MostlyCoraGrace/EurorackButtonBoard/Docs/Logs/Log-1_001.jpg

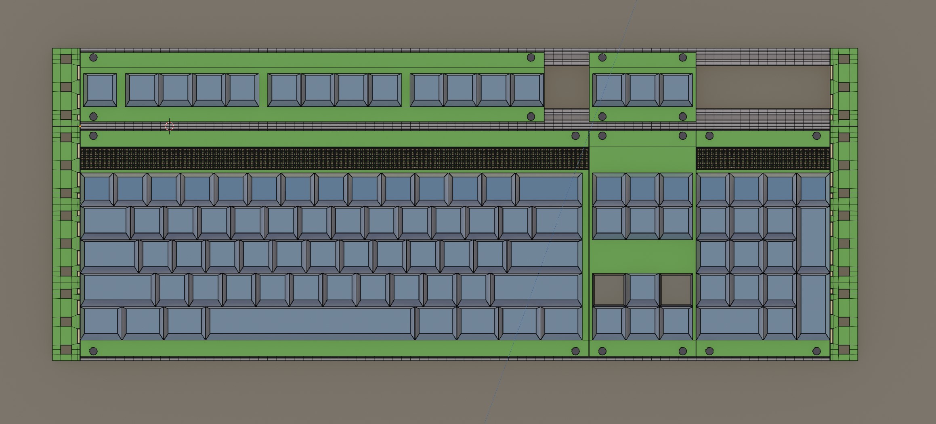
Docs/Logs/Log-1_001.jpg
