MostlyCoraGrace/EurorackButtonBoard/Docs/Logs/Log-2_001.jpg

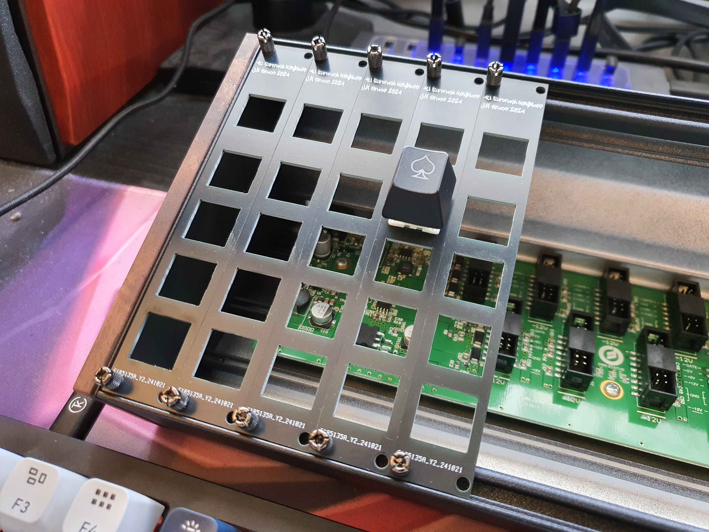
Docs/Logs/Log-2_001.jpg
