MostlyCoraGrace/EurorackButtonBoard/Docs/Logs/Log-3_001.jpg

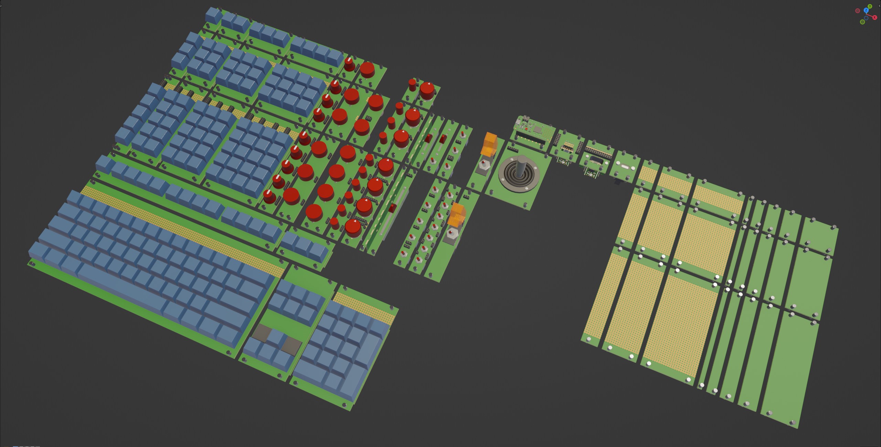
Docs/Logs/Log-3_001.jpg
