MostlyCoraGrace/EurorackButtonBoard/Docs/Logs/Log-3_002.jpg

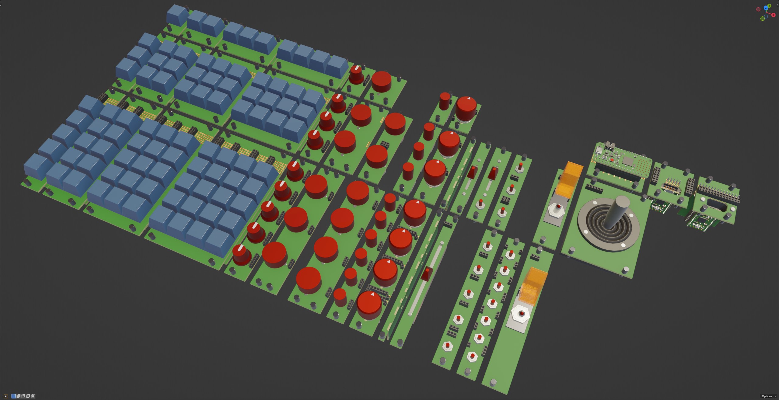
Docs/Logs/Log-3_002.jpg
