MostlyCoraGrace/EurorackButtonBoard/Docs/Logs/Log-4_001.jpg

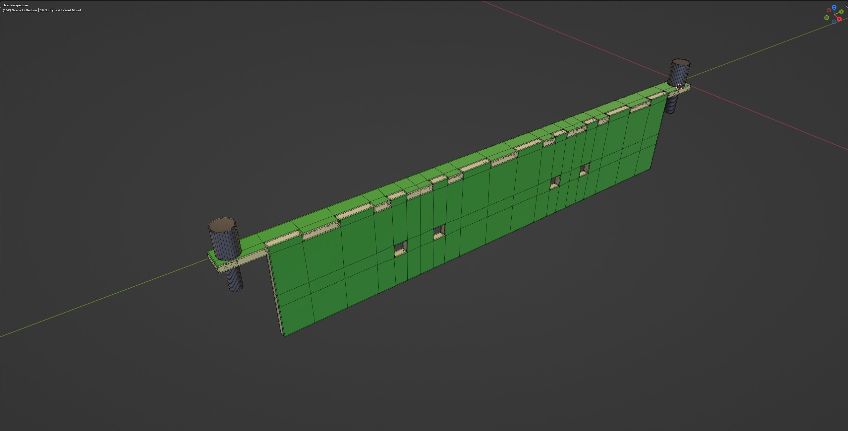
Docs/Logs/Log-4_001.jpg
