MostlyCoraGrace/EurorackButtonBoard/Docs/Logs/Log-4_002.jpg

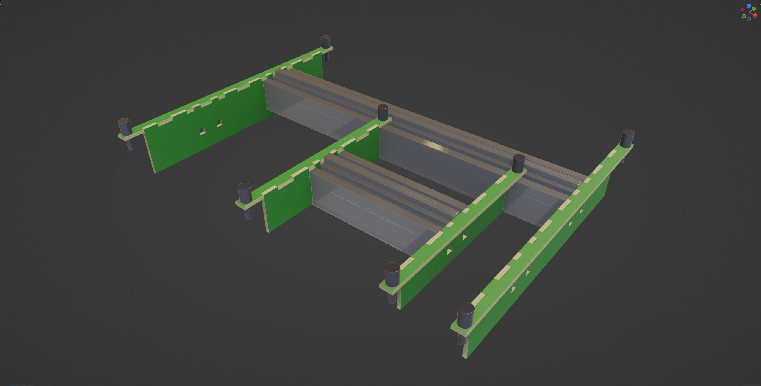
Docs/Logs/Log-4_002.jpg
