MostlyCoraGrace/EurorackButtonBoard/Docs/Logs/Log-4_003.jpg

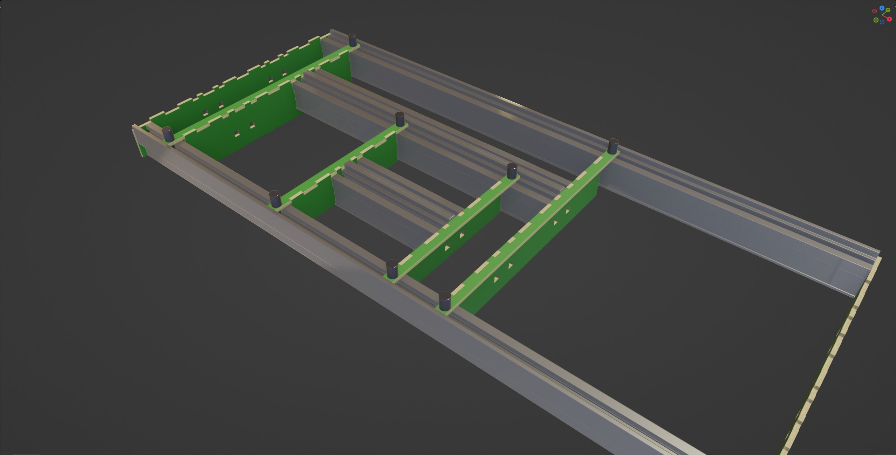
Docs/Logs/Log-4_003.jpg
