MostlyCoraGrace/EurorackButtonBoard/Docs/Logs/Log-6_001.jpg

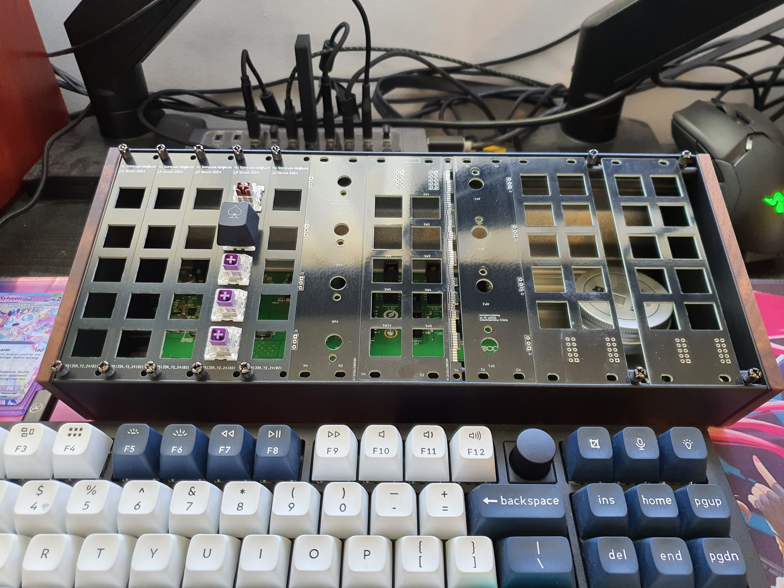
Docs/Logs/Log-6_001.jpg
