MostlyCoraGrace/EurorackButtonBoard/Docs/Logs/Log-6_002.jpg

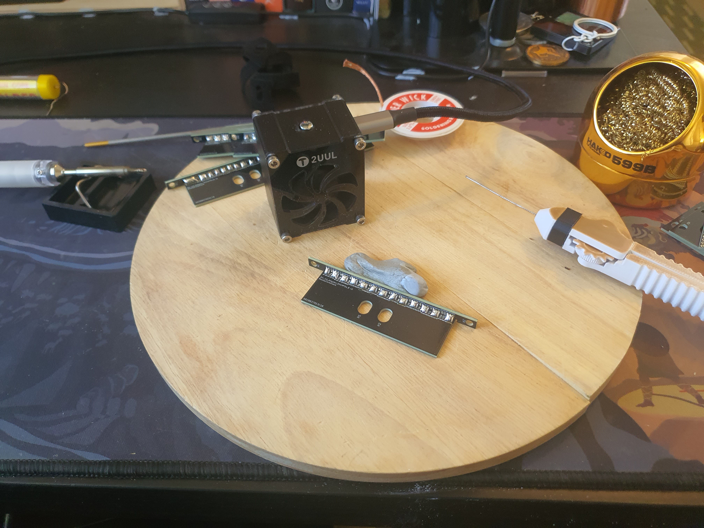
Docs/Logs/Log-6_002.jpg
