MostlyCoraGrace/EurorackButtonBoard/Docs/Logs/Log-6_003.jpg

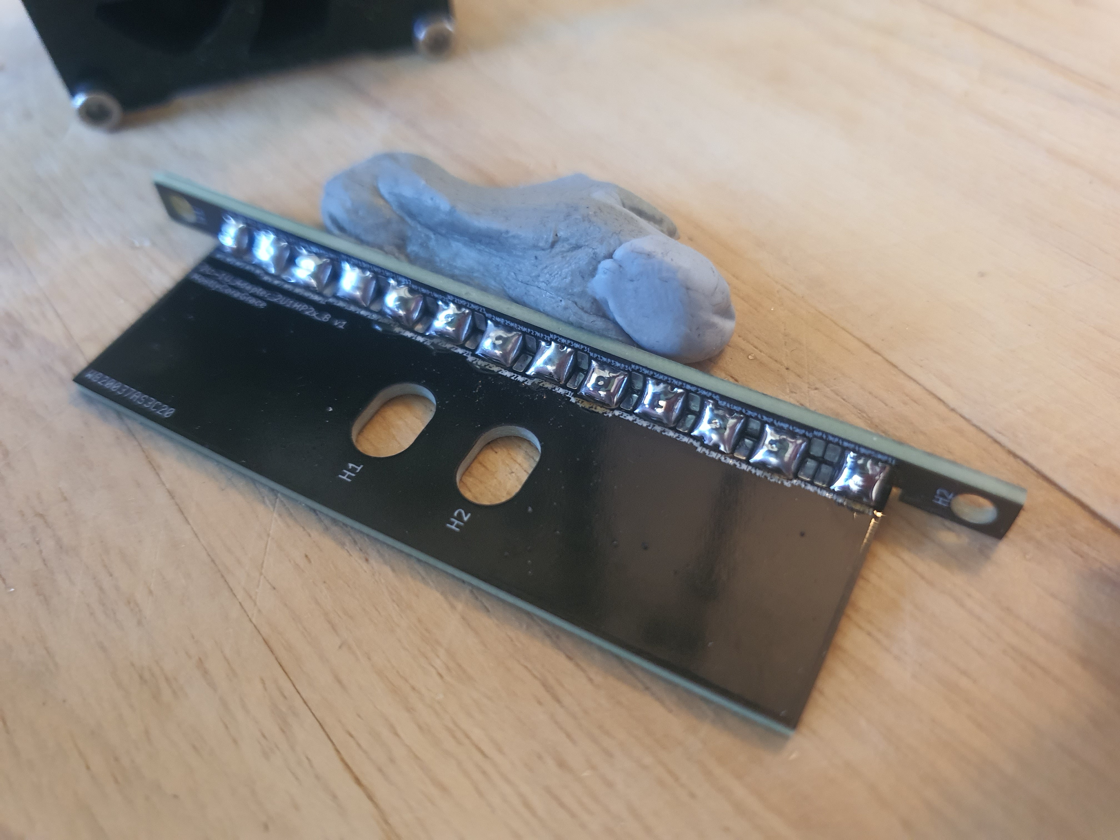
Docs/Logs/Log-6_003.jpg
