MostlyCoraGrace/EurorackButtonBoard/Docs/Logs/Log-6_004.jpg

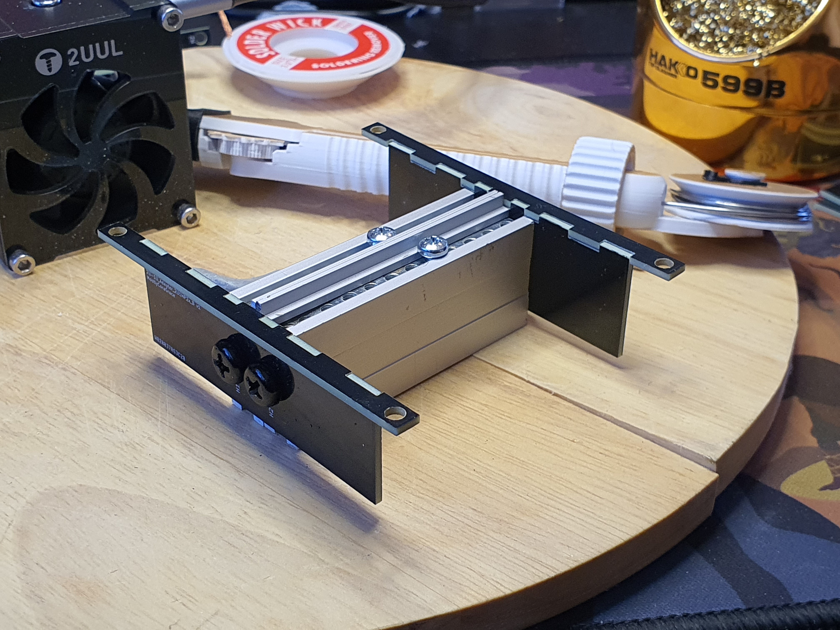
Docs/Logs/Log-6_004.jpg
