MostlyCoraGrace/EurorackButtonBoard/Docs/Logs/Log-6_005.jpg

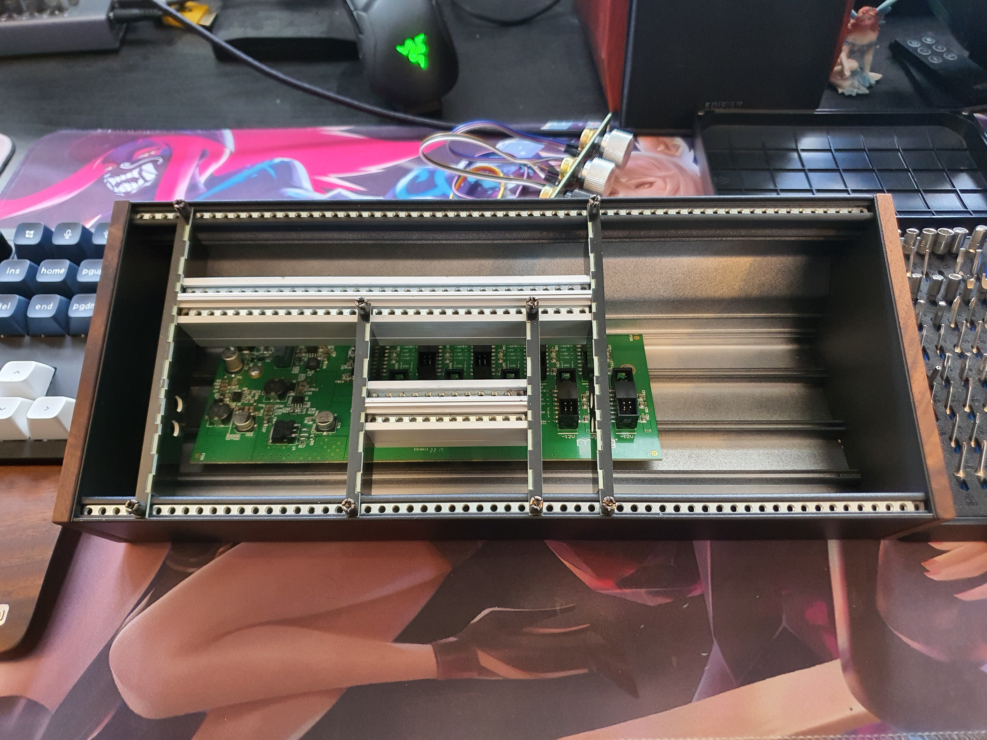
Docs/Logs/Log-6_005.jpg
