MostlyCoraGrace/EurorackButtonBoard/Docs/Logs/Log-6_006.jpg

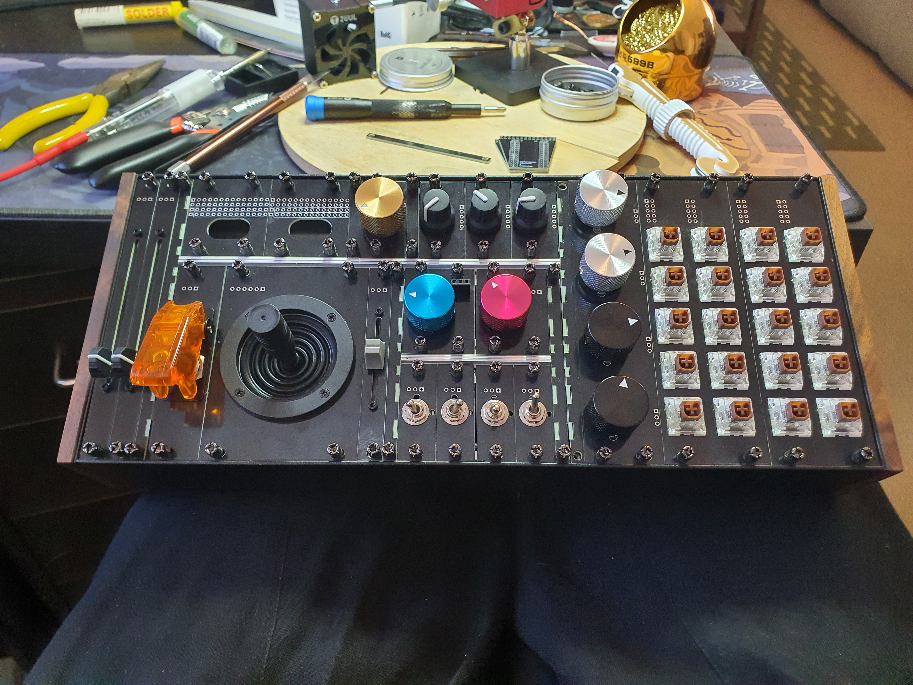
Docs/Logs/Log-6_006.jpg
