MostlyCoraGrace/EurorackButtonBoard/Docs/Logs/Log-6_007.jpg

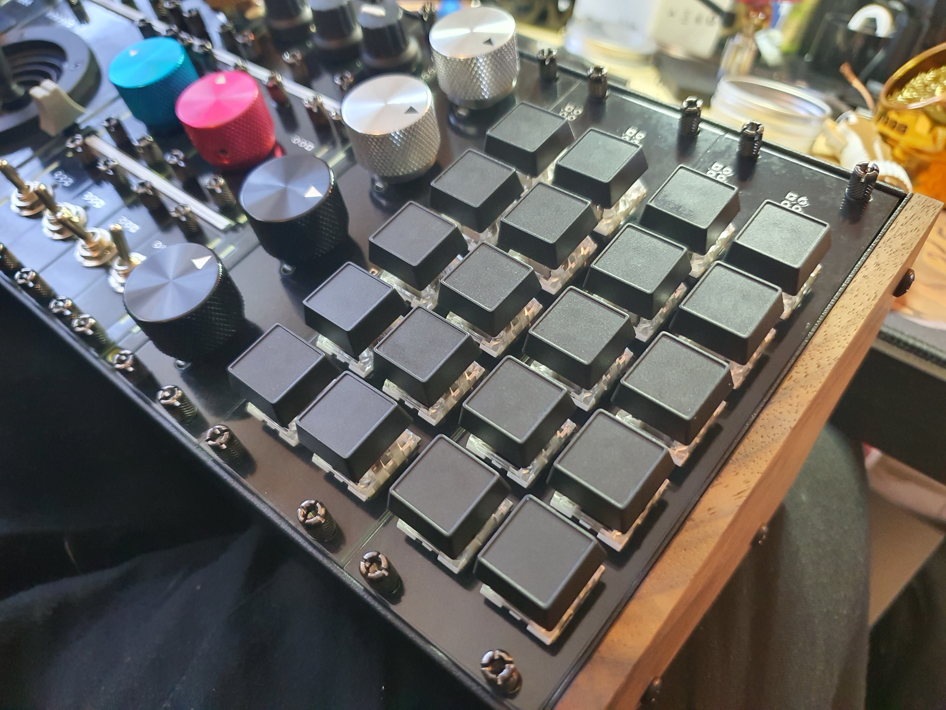
Docs/Logs/Log-6_007.jpg
