MostlyCoraGrace/EurorackButtonBoard/Docs/Logs/Log-6_008.jpg

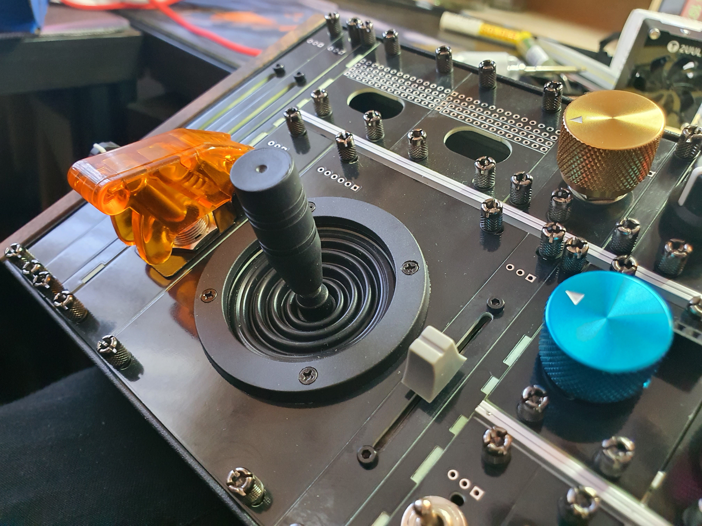
Docs/Logs/Log-6_008.jpg
