MostlyCoraGrace/EurorackButtonBoard/Docs/Logs/Log-6_009.jpg

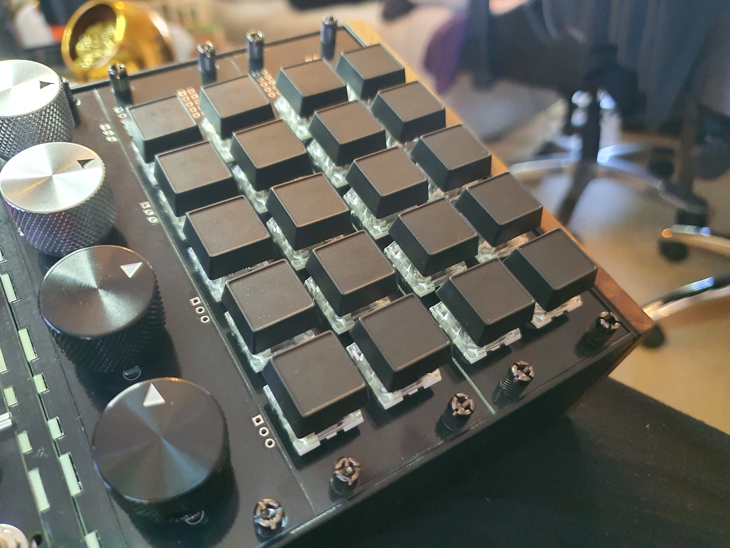
Docs/Logs/Log-6_009.jpg
