MostlyCoraGrace/EurorackButtonBoard/Docs/Logs/Log-6_010.jpg

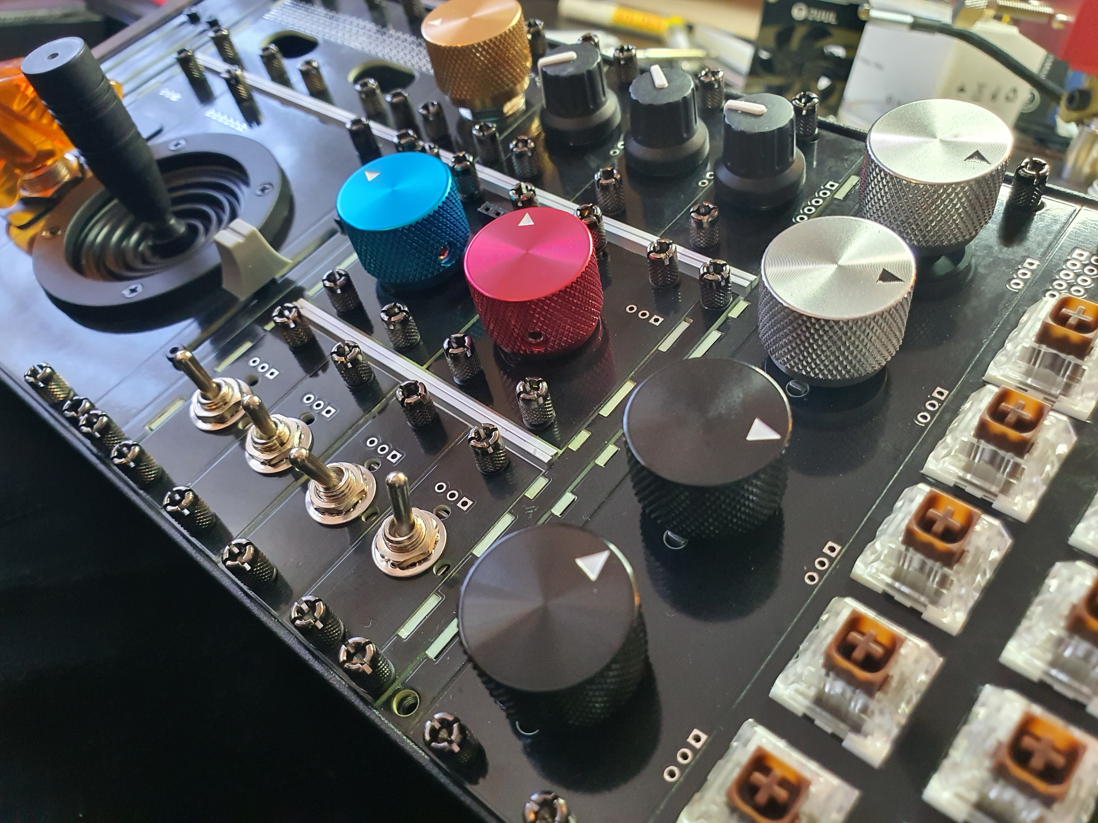
Docs/Logs/Log-6_010.jpg
