MostlyCoraGrace/EurorackButtonBoard/Docs/Logs/Log-6_011.jpg

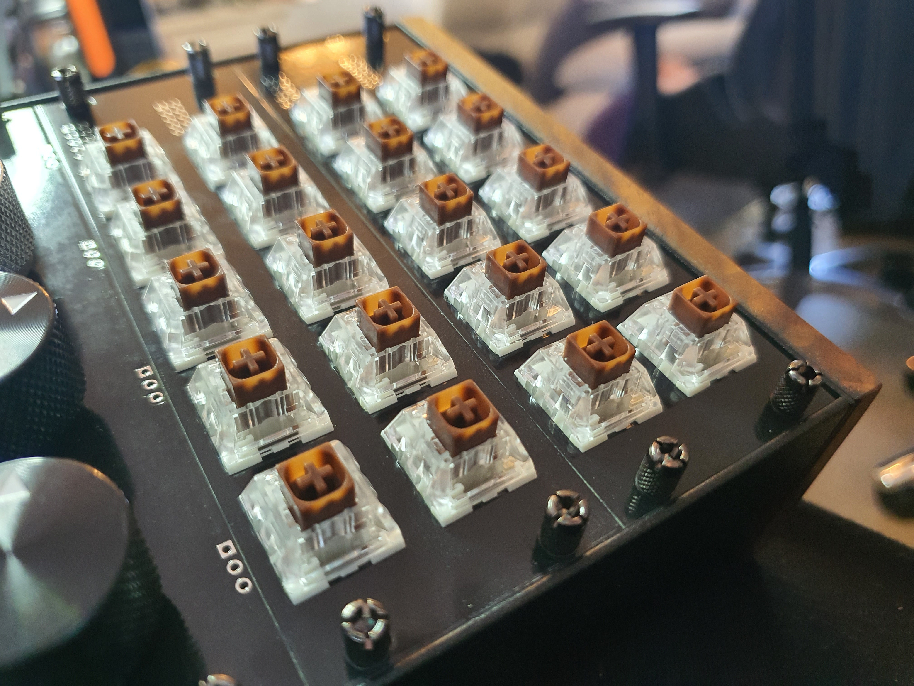
Docs/Logs/Log-6_011.jpg
