MostlyCoraGrace/EurorackButtonBoard/Docs/Logs/Log-6_012.jpg

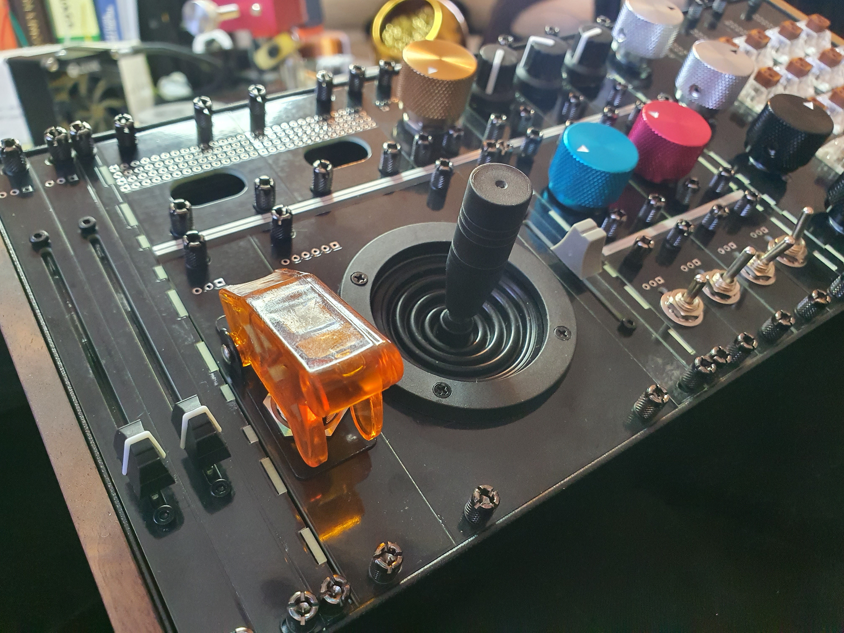
Docs/Logs/Log-6_012.jpg
