MostlyCoraGrace/EurorackButtonBoard/Docs/Logs/Log-6_013.jpg

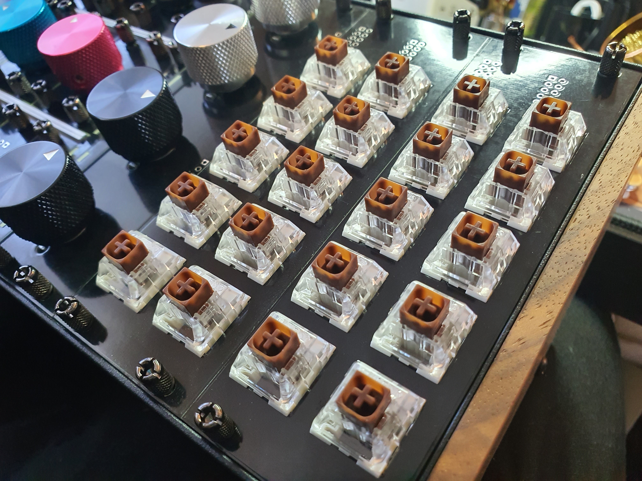
Docs/Logs/Log-6_013.jpg
