MostlyCoraGrace/EurorackButtonBoard/Docs/Logs/Log-6_014.jpg

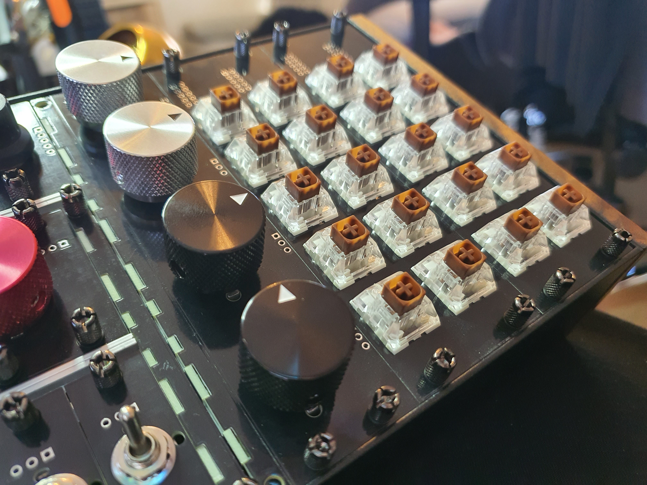
Docs/Logs/Log-6_014.jpg
