MostlyCoraGrace/EurorackButtonBoard/Docs/Logs/Log-6_015.jpg

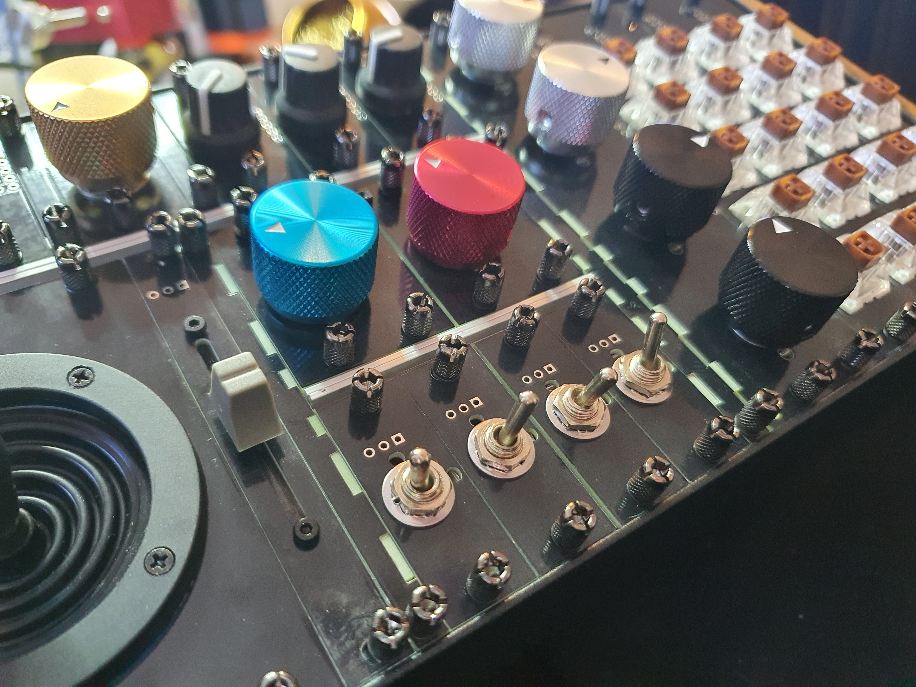
Docs/Logs/Log-6_015.jpg
