MostlyCoraGrace/EurorackButtonBoard/Docs/Logs/Log-7_001.jpg

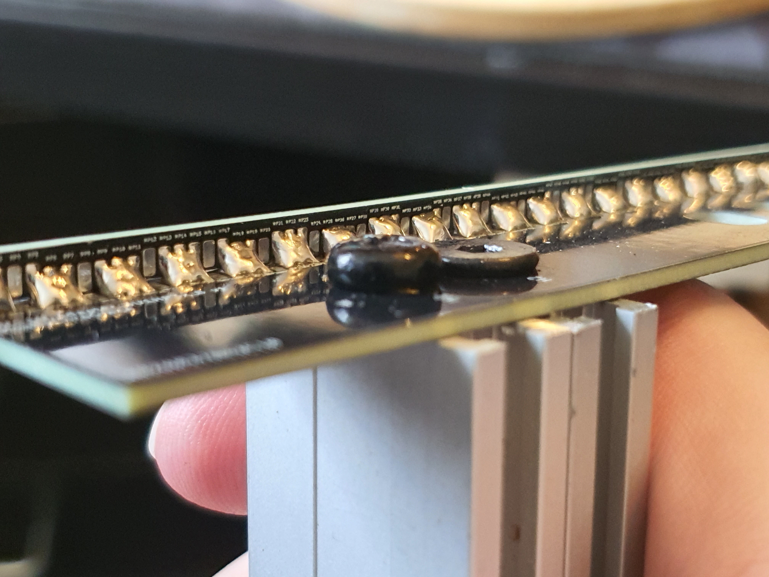
Docs/Logs/Log-7_001.jpg
