MostlyCoraGrace/EurorackButtonBoard/Docs/Logs/Log-7_002.jpg

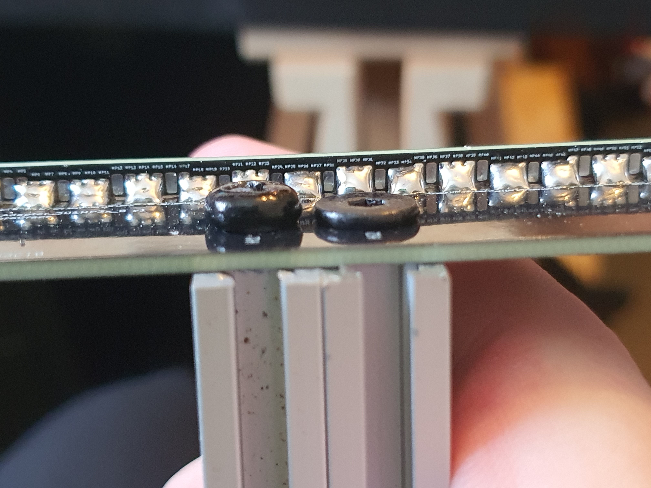
Docs/Logs/Log-7_002.jpg
