MostlyCoraGrace/EurorackButtonBoard/Docs/Logs/Log-7_003.jpg

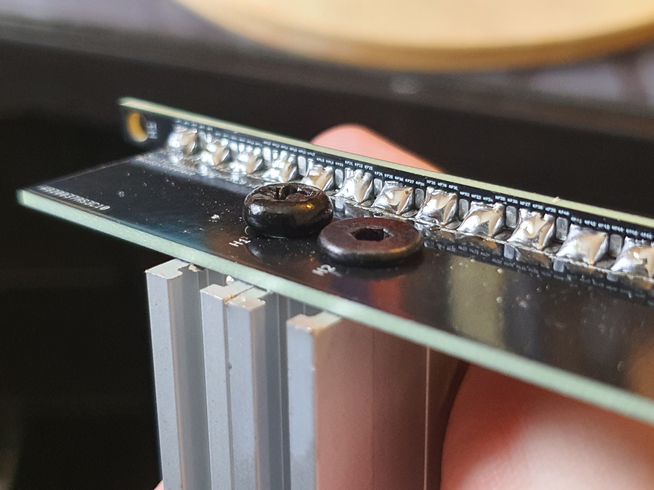
Docs/Logs/Log-7_003.jpg
