MostlyCoraGrace/EurorackButtonBoard/Docs/Logs/Log-7_004.jpg

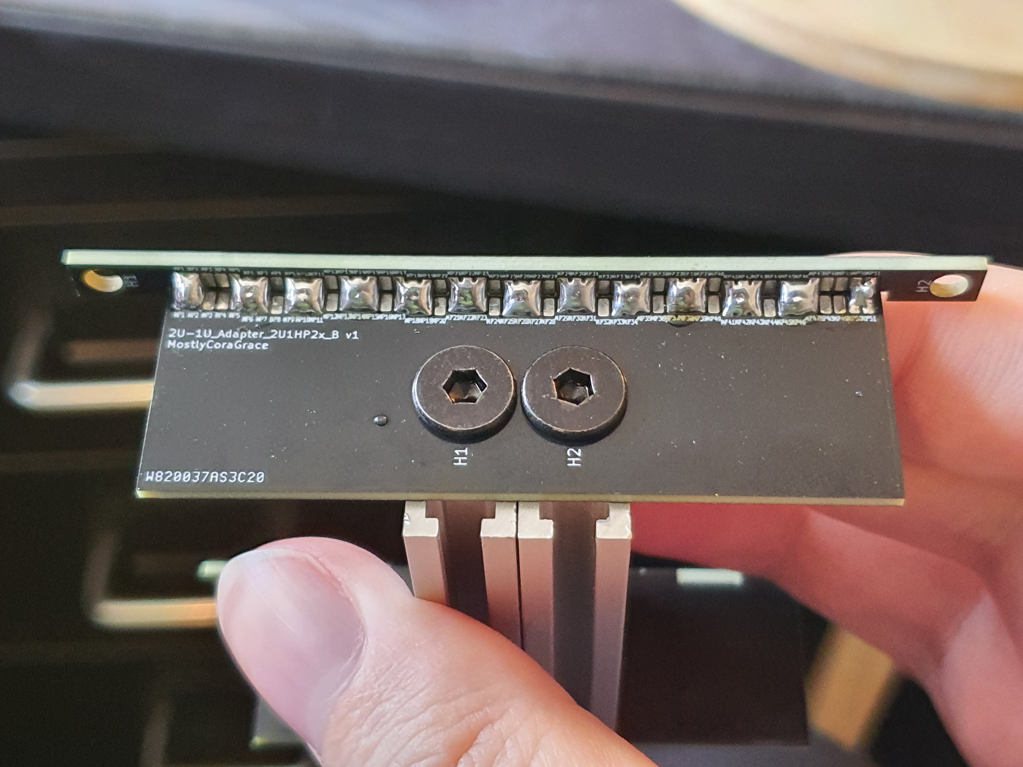
Docs/Logs/Log-7_004.jpg
