MostlyCoraGrace/EurorackButtonBoard/Docs/Logs/Log-7_005.jpg

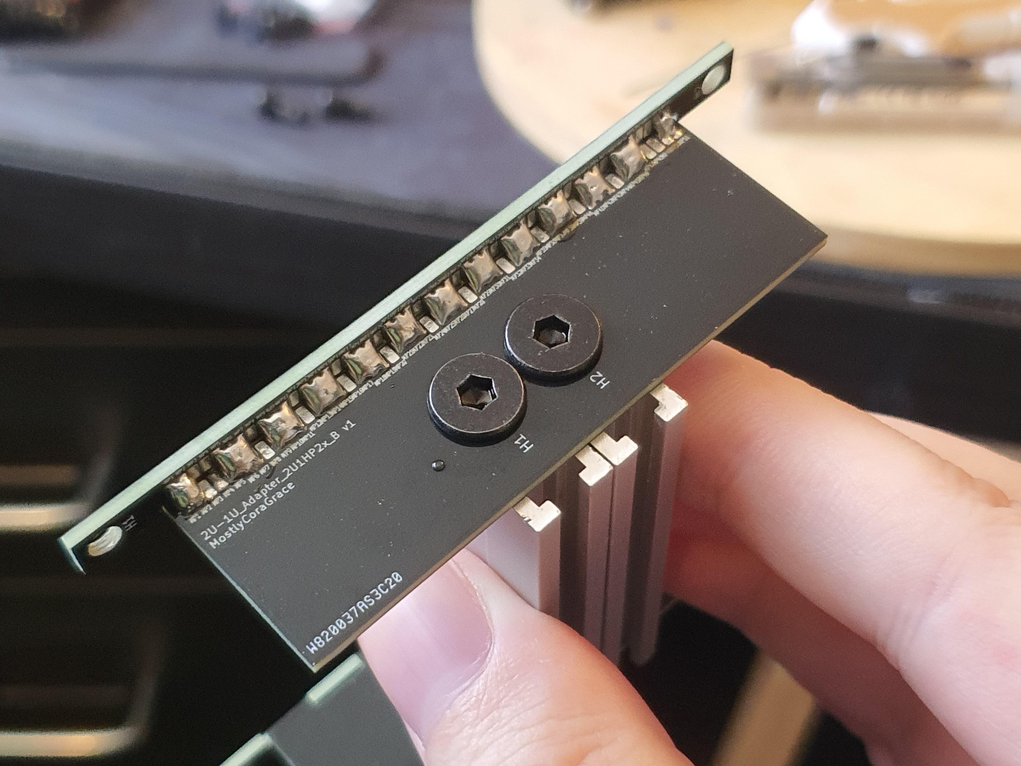
Docs/Logs/Log-7_005.jpg
