MostlyCoraGrace/EurorackButtonBoard/Docs/Logs/Log-7_006.jpg

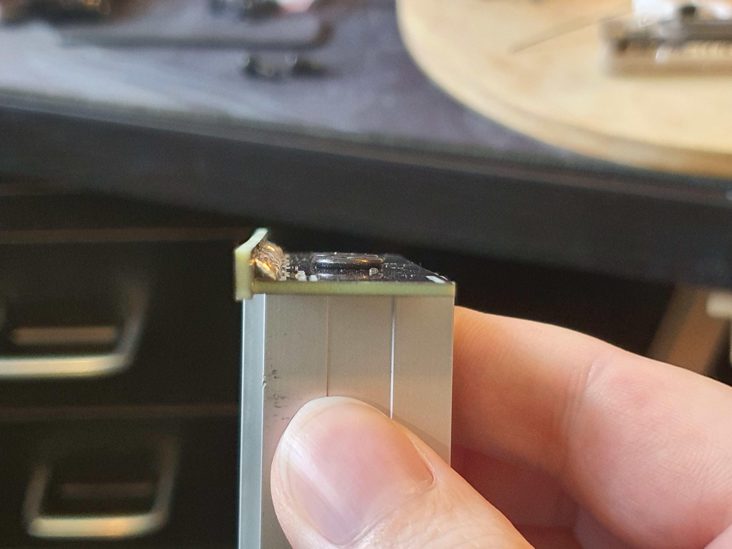
Docs/Logs/Log-7_006.jpg
