MostlyCoraGrace/EurorackButtonBoard/Docs/Logs/Log-7_007.jpg

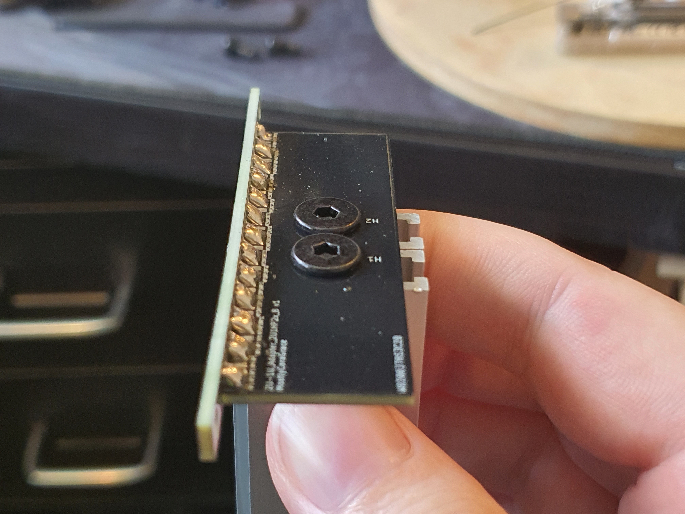
Docs/Logs/Log-7_007.jpg
