MostlyCoraGrace/EurorackButtonBoard/Docs/Logs/Log-8_001.jpg

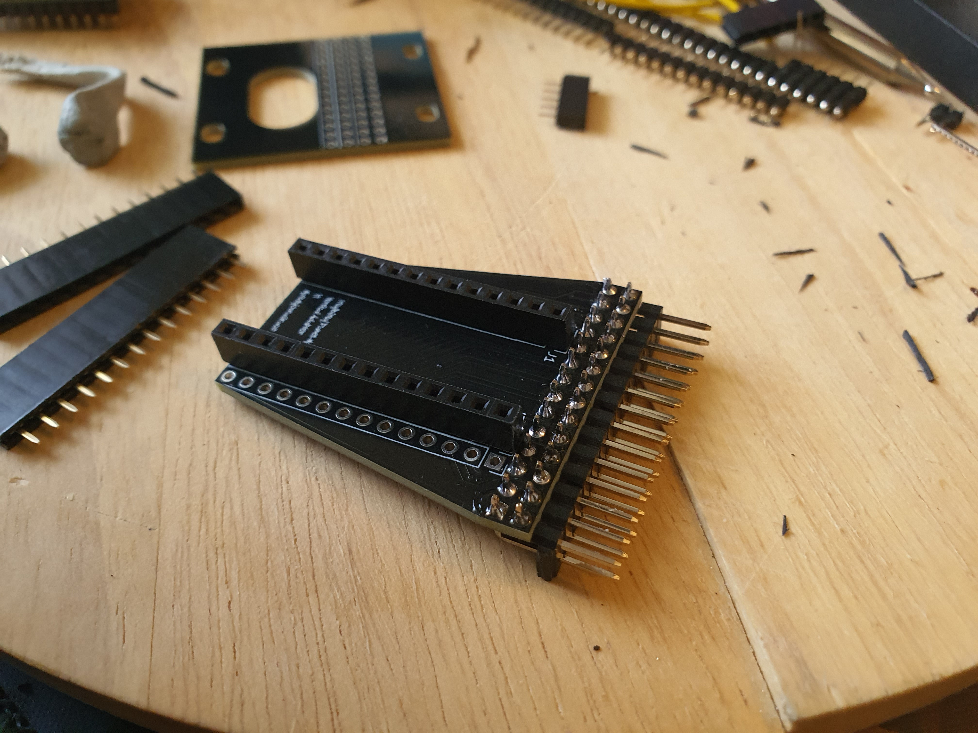
Docs/Logs/Log-8_001.jpg
