MostlyCoraGrace/EurorackButtonBoard/Docs/Logs/Log-8_002.jpg

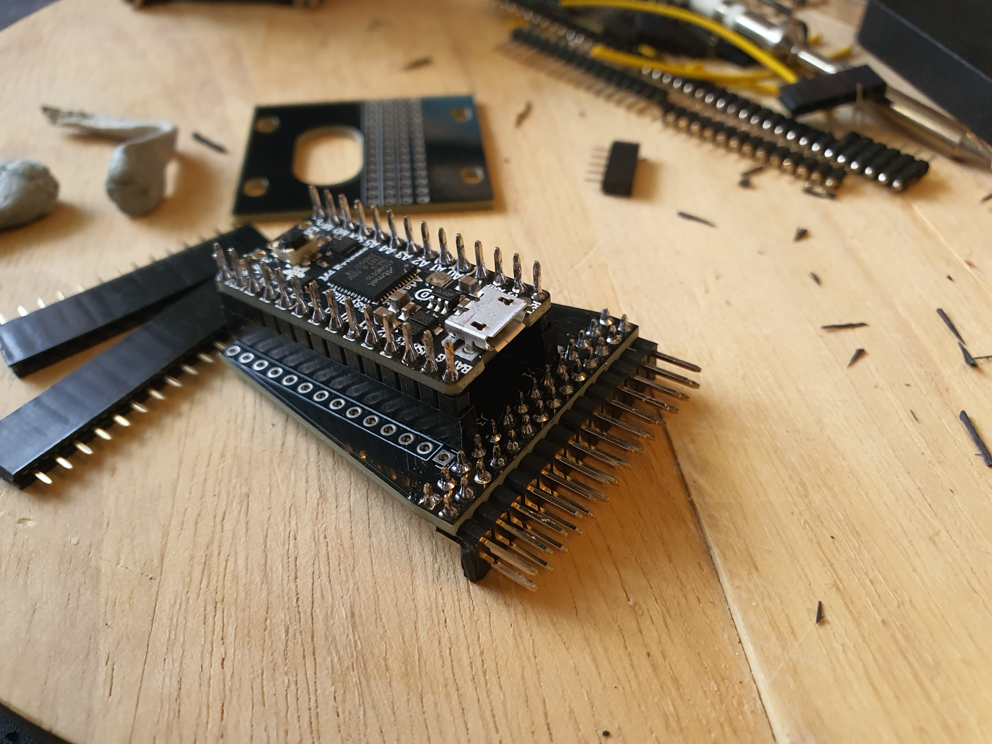
Docs/Logs/Log-8_002.jpg
