MostlyCoraGrace/EurorackButtonBoard/Docs/Logs/Log-8_003.jpg

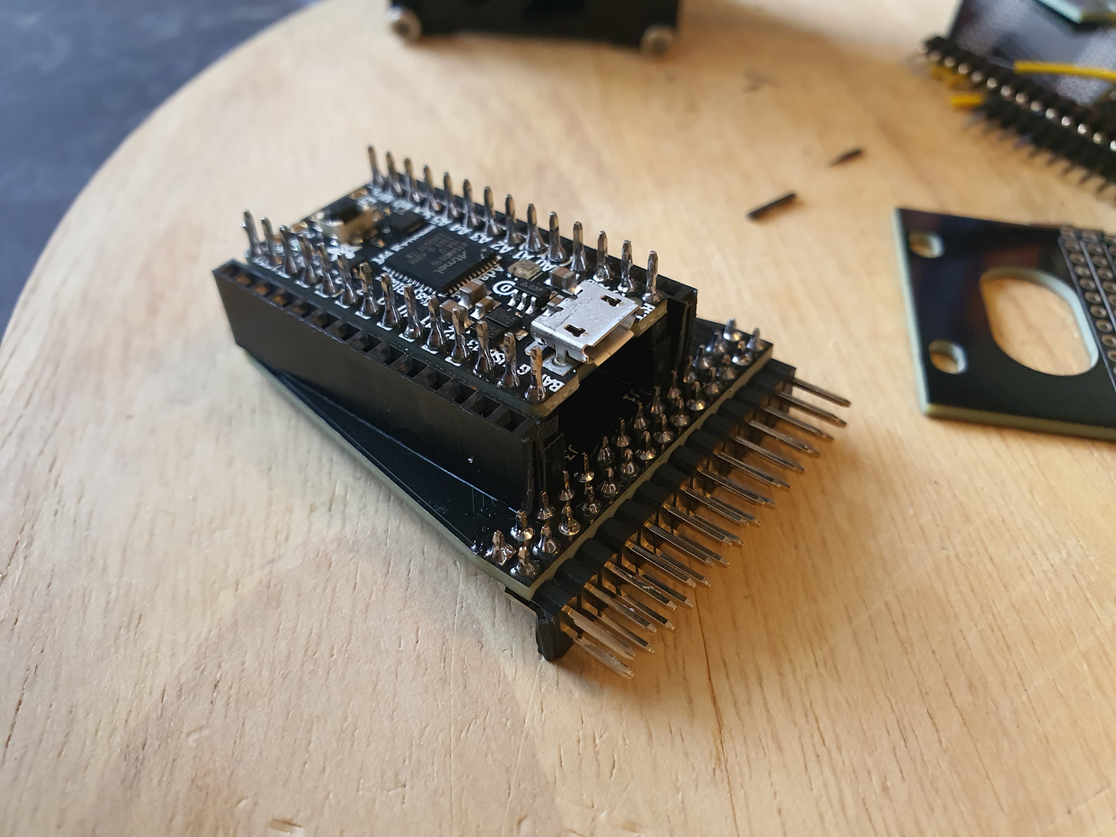
Docs/Logs/Log-8_003.jpg
