MostlyCoraGrace/EurorackButtonBoard/Docs/Logs/Log-8_004.jpg

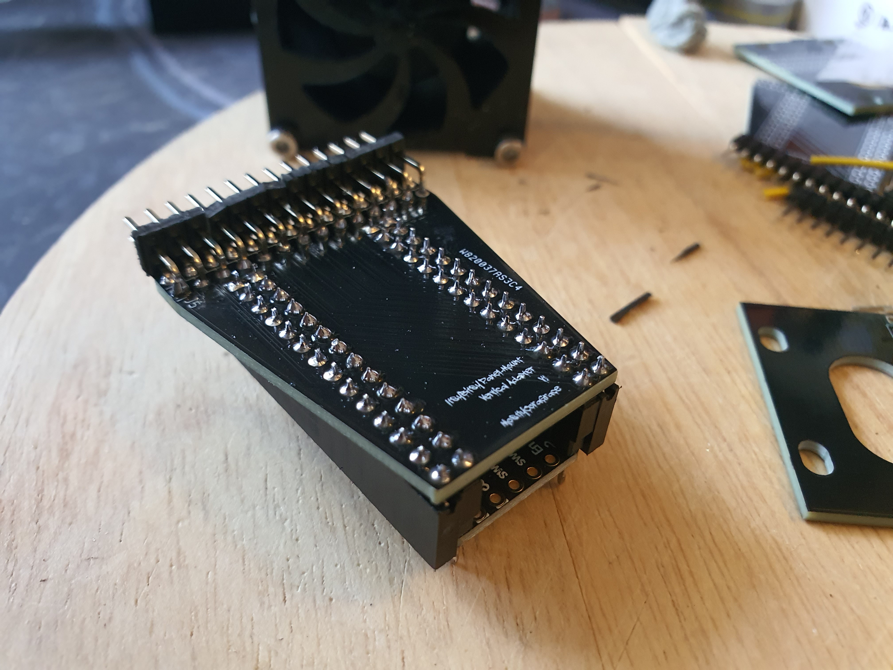
Docs/Logs/Log-8_004.jpg
