MostlyCoraGrace/EurorackButtonBoard/Docs/Logs/Log-8_005.jpg

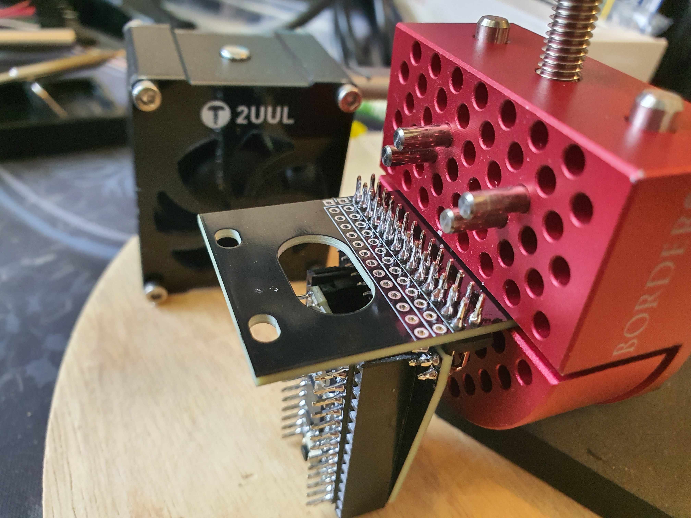
Docs/Logs/Log-8_005.jpg
