MostlyCoraGrace/EurorackButtonBoard/Docs/Logs/Log-8_006.jpg

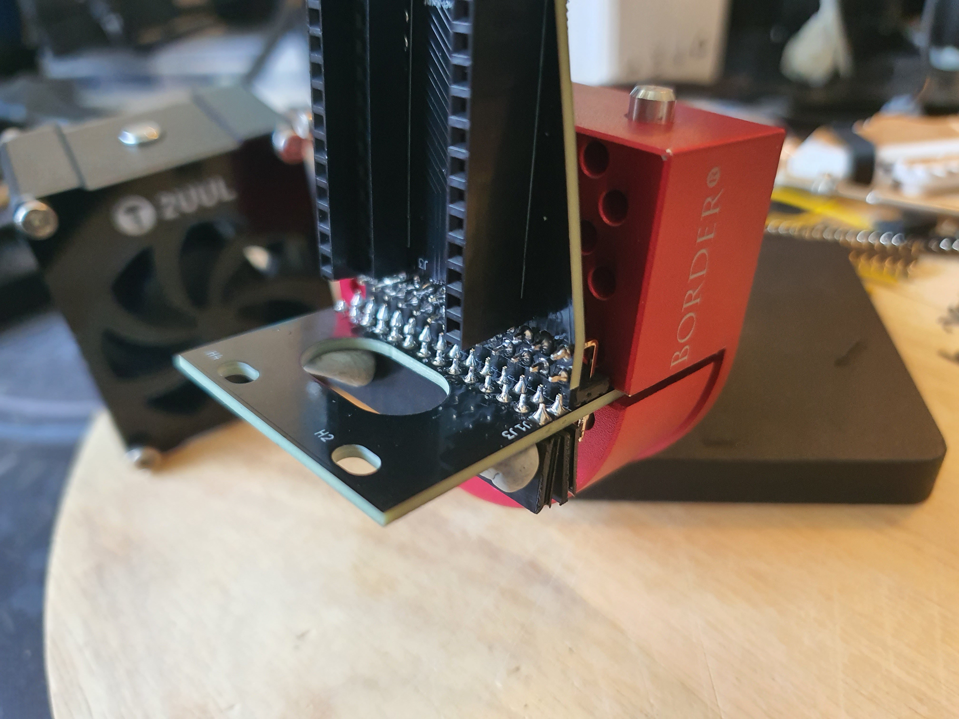
Docs/Logs/Log-8_006.jpg
