MostlyCoraGrace/EurorackButtonBoard/Docs/Logs/Log-8_007.jpg

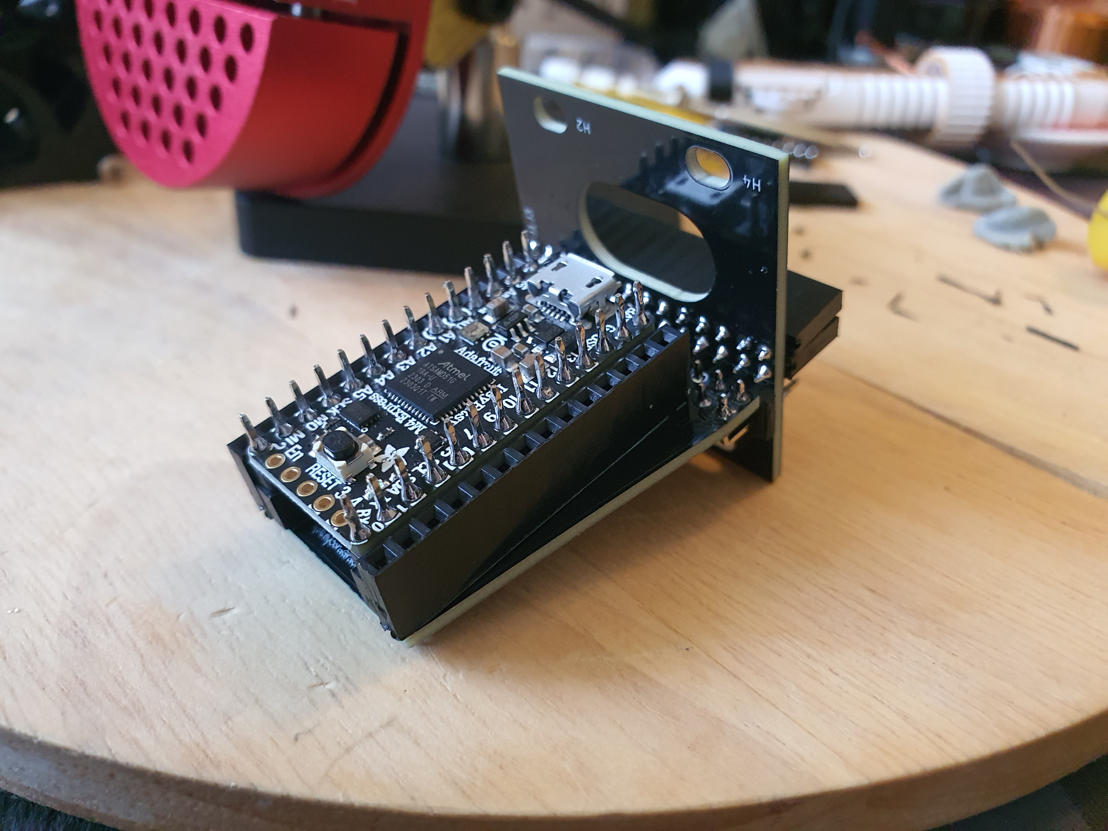
Docs/Logs/Log-8_007.jpg
