MostlyCoraGrace/EurorackButtonBoard/Docs/Logs/Log-8_008.jpg

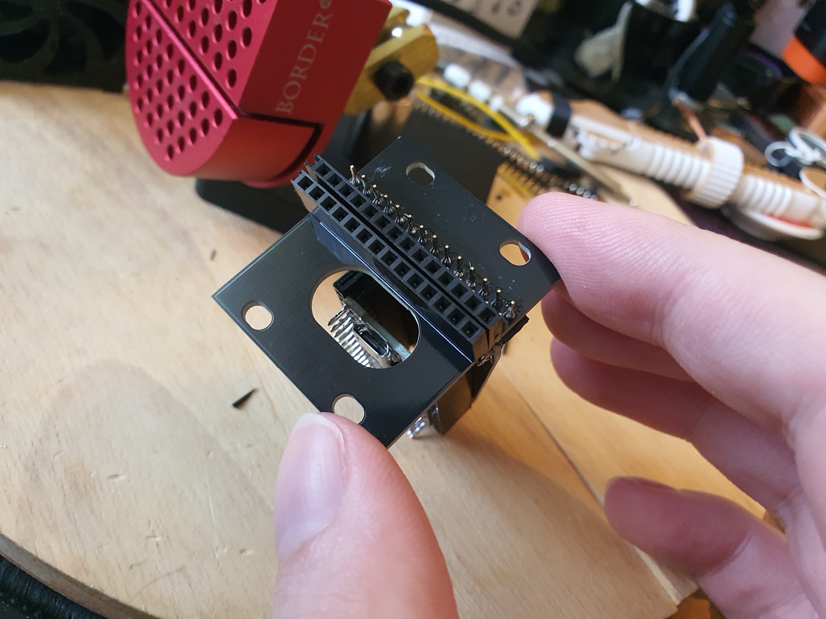
Docs/Logs/Log-8_008.jpg
