MostlyCoraGrace/EurorackButtonBoard/Docs/Logs/Log-8_009.jpg

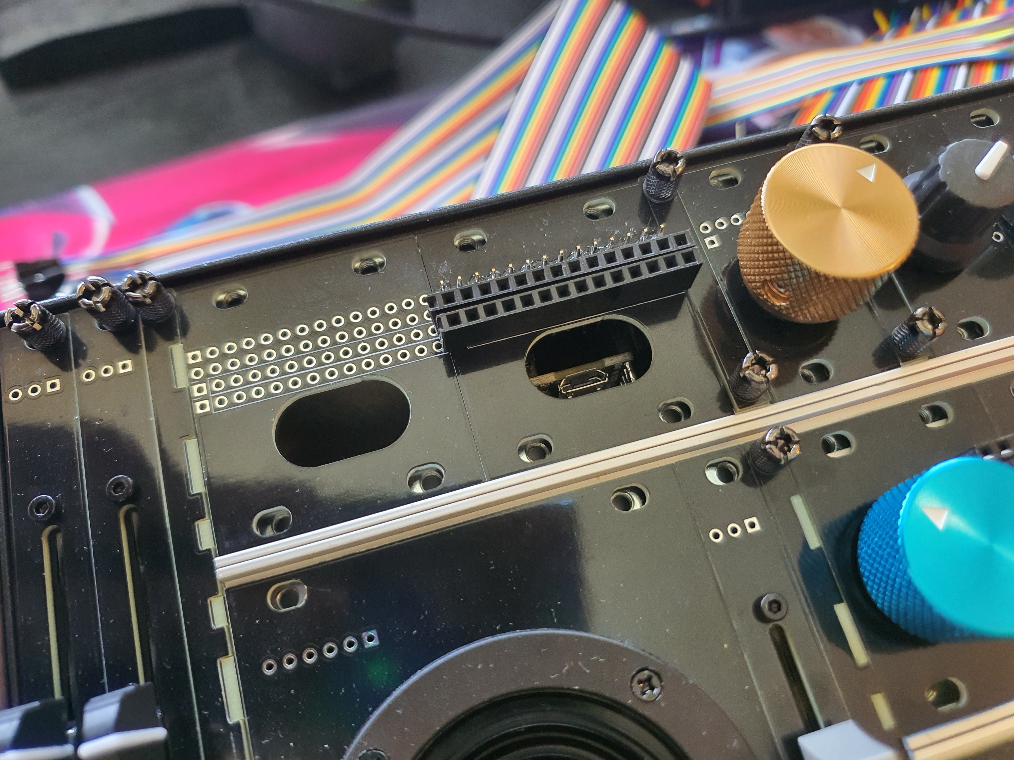
Docs/Logs/Log-8_009.jpg
