MostlyCoraGrace/EurorackButtonBoard/Docs/Logs/Log-8_010.jpg

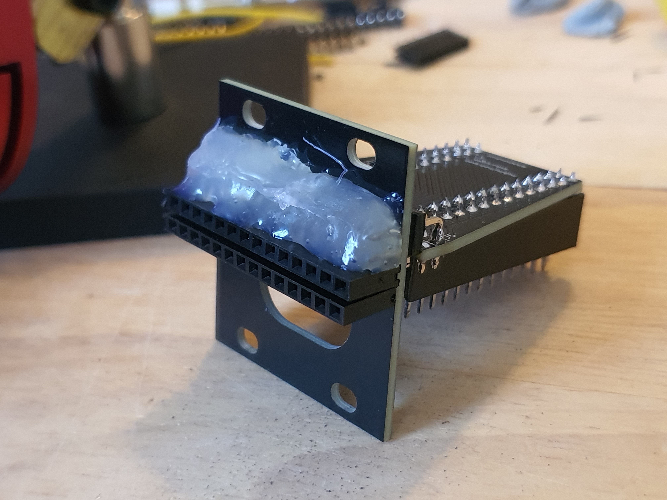
Docs/Logs/Log-8_010.jpg
