MostlyCoraGrace/EurorackButtonBoard/Docs/Logs/Log-8_011.jpg

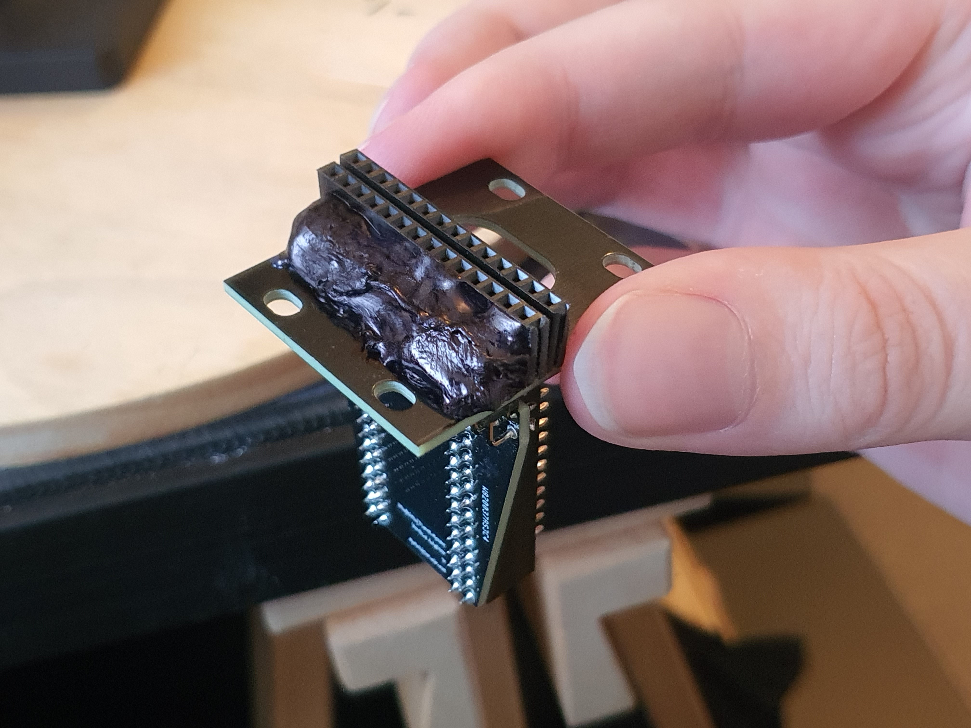
Docs/Logs/Log-8_011.jpg
