MostlyCoraGrace/EurorackButtonBoard/Docs/Logs/Log-9_001.jpg

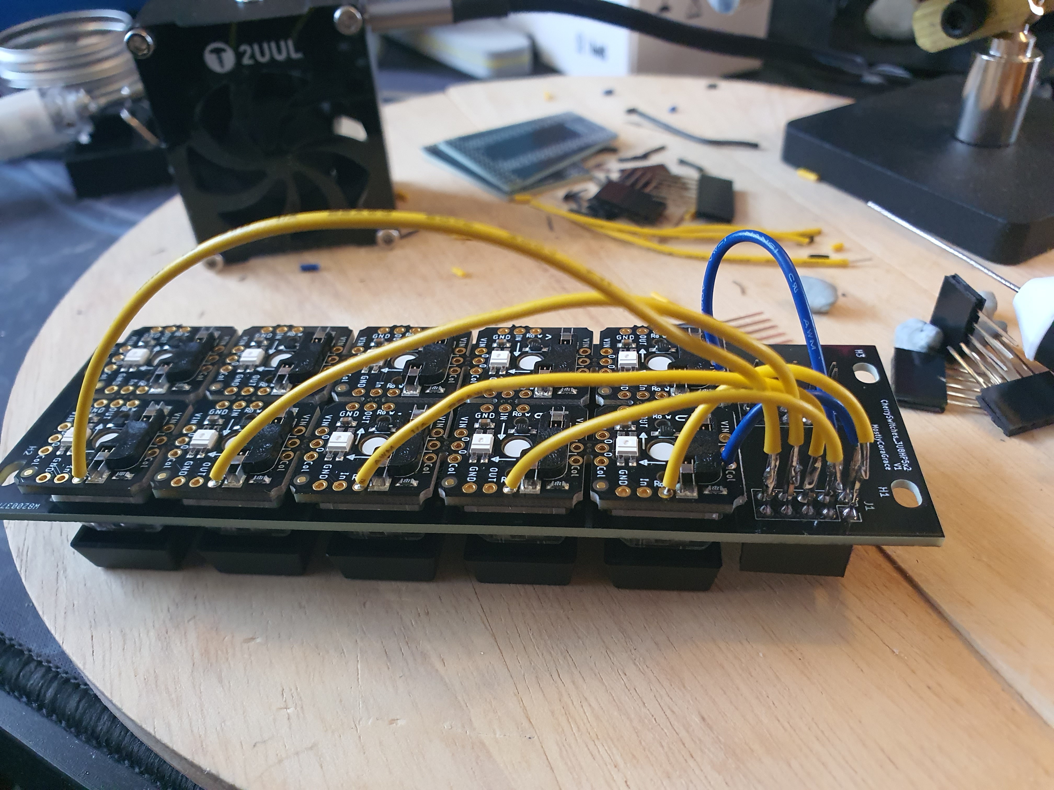
Docs/Logs/Log-9_001.jpg
