MostlyCoraGrace/EurorackButtonBoard/Docs/Logs/Log-9_002.jpg

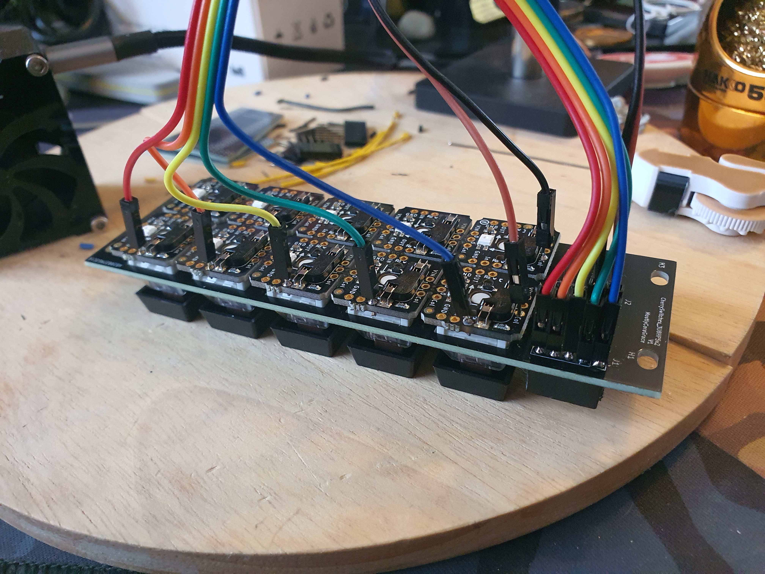
Docs/Logs/Log-9_002.jpg
