MostlyCoraGrace/EurorackButtonBoard/Docs/Logs/Log-9_003.jpg

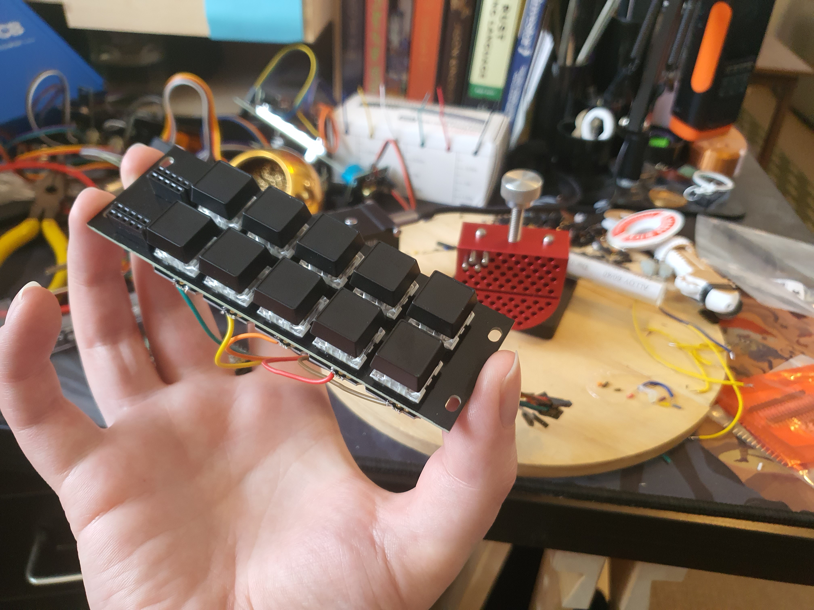
Docs/Logs/Log-9_003.jpg
