MostlyCoraGrace/EurorackButtonBoard/Docs/Logs/Log-9_004.jpg

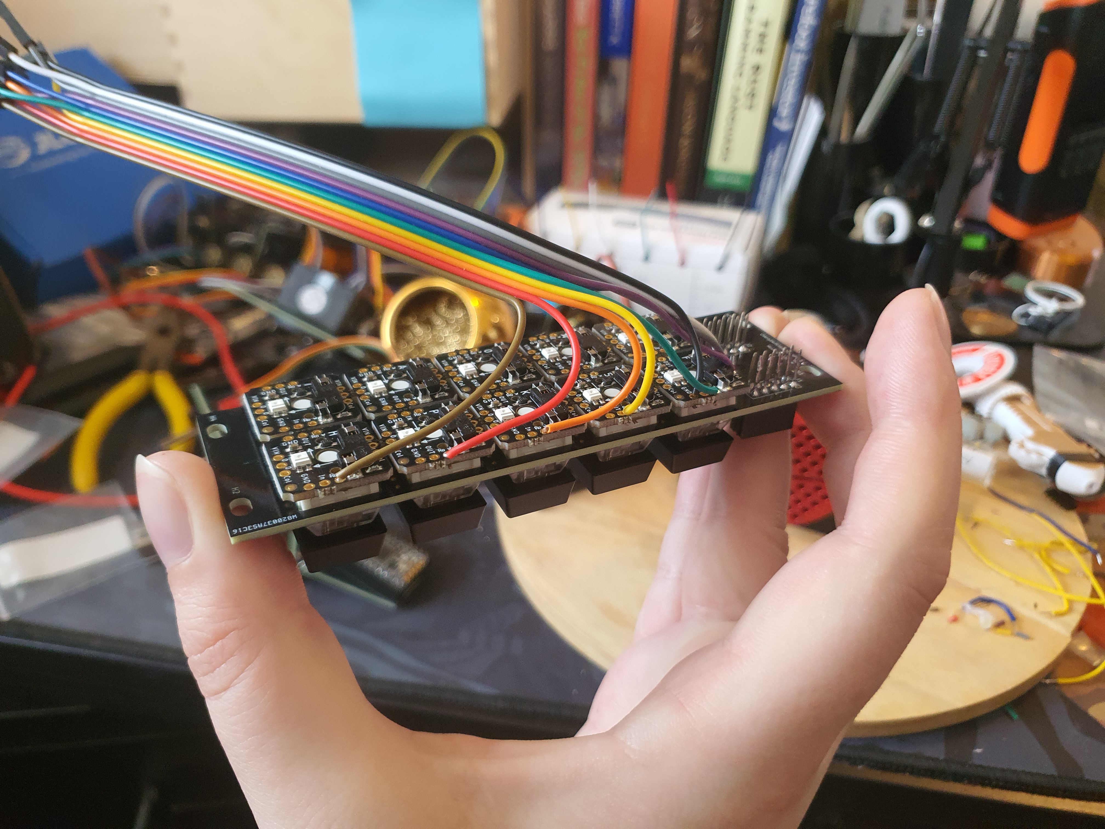
Docs/Logs/Log-9_004.jpg
