MostlyCoraGrace/EurorackButtonBoard/Docs/Logs/Log-9_005.jpg

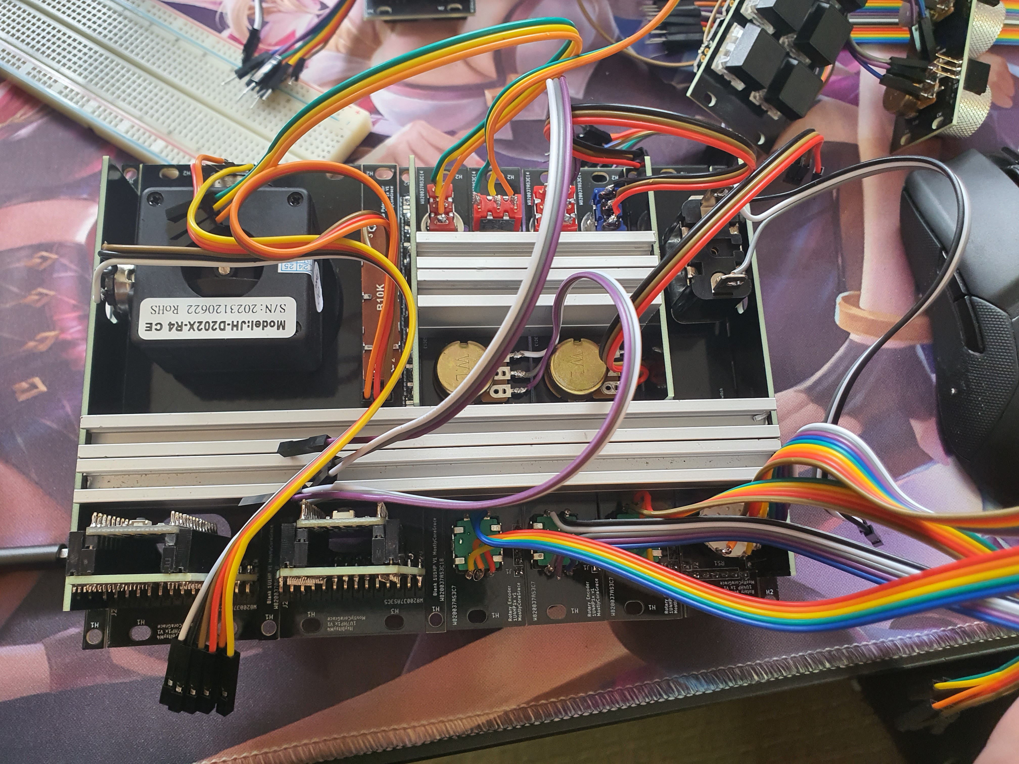
Docs/Logs/Log-9_005.jpg
