MostlyCoraGrace/EurorackButtonBoard/Docs/Logs/Log-9_006.jpg

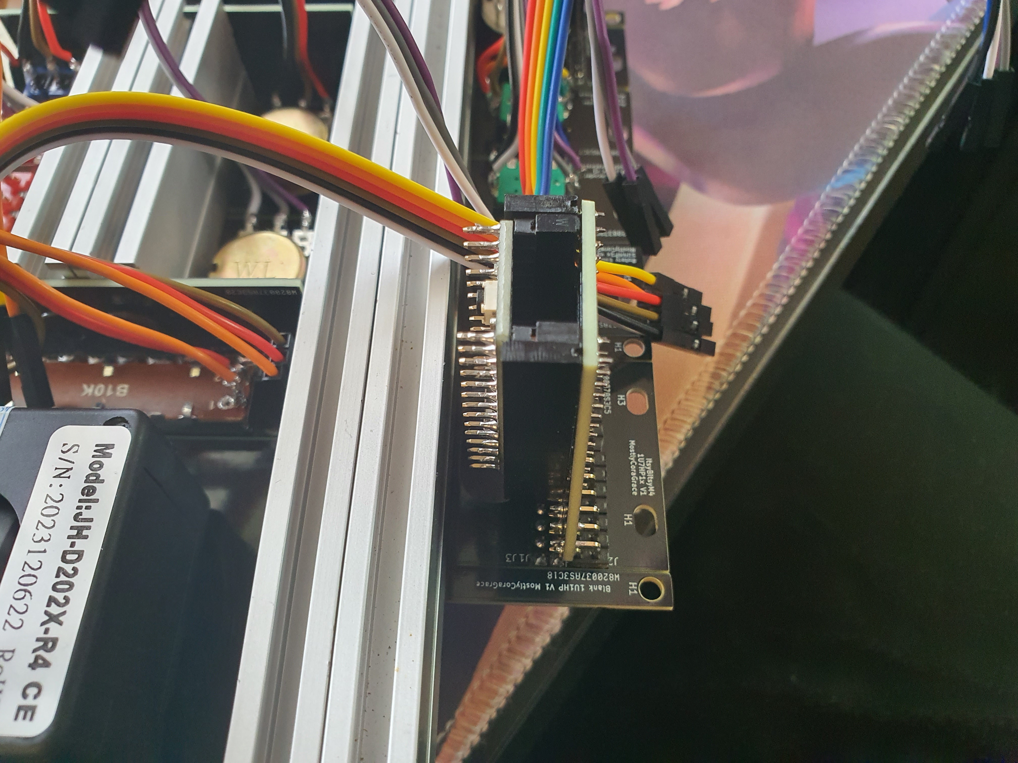
Docs/Logs/Log-9_006.jpg
