MostlyCoraGrace/EurorackButtonBoard/Docs/Logs/Log-9_007.jpg

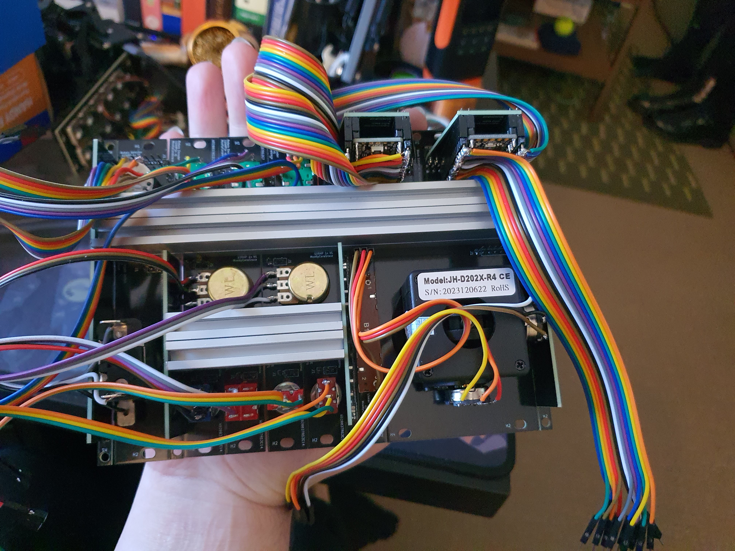
Docs/Logs/Log-9_007.jpg
