MostlyCoraGrace/EurorackButtonBoard/Docs/Logs/Log-9_008.jpg

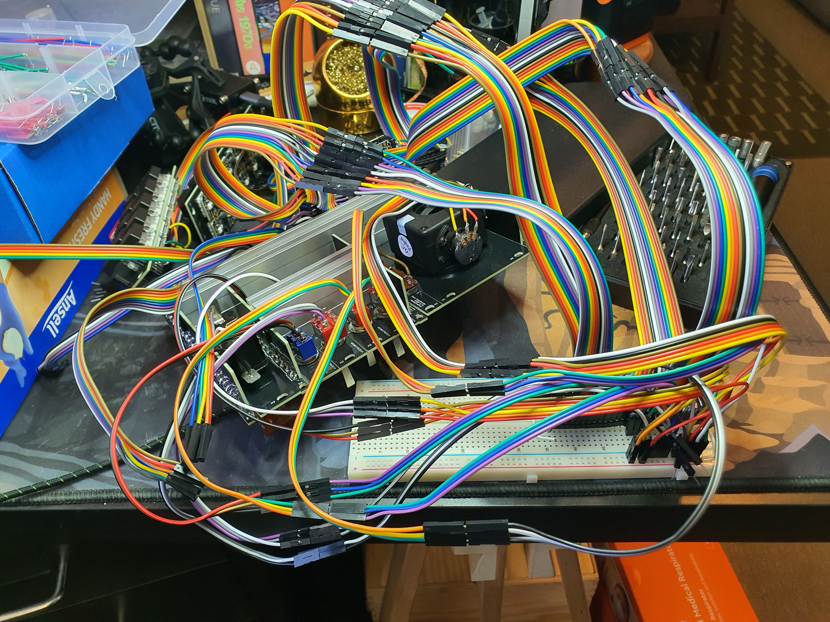
Docs/Logs/Log-9_008.jpg
