MostlyCoraGrace/EurorackButtonBoard/Docs/Logs/Log-9_009.jpg

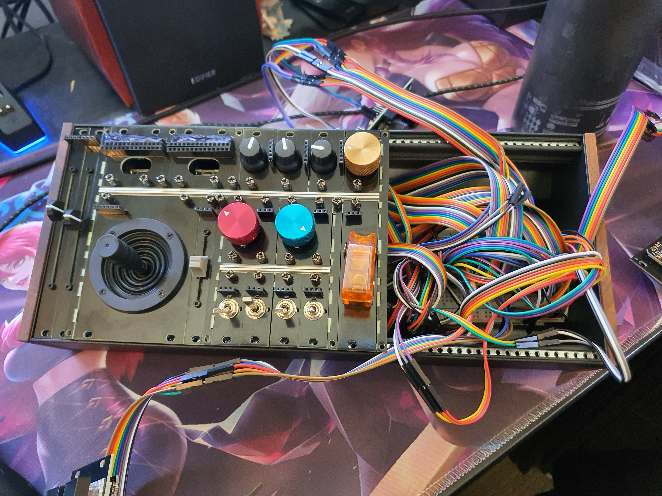
Docs/Logs/Log-9_009.jpg
