MostlyCoraGrace/EurorackButtonBoard/Docs/Logs/Log-9_010.jpg

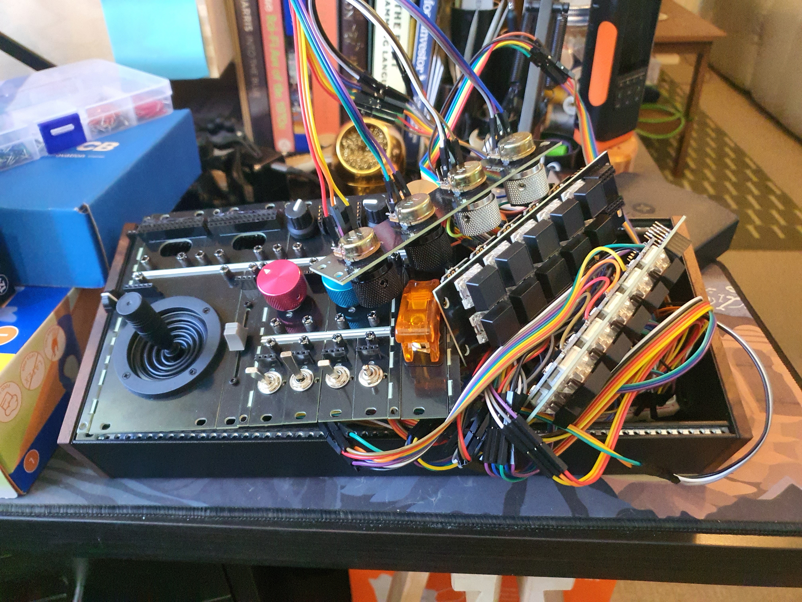
Docs/Logs/Log-9_010.jpg
