MostlyCoraGrace/EurorackButtonBoard/Docs/Logs/Log-9_011.jpg

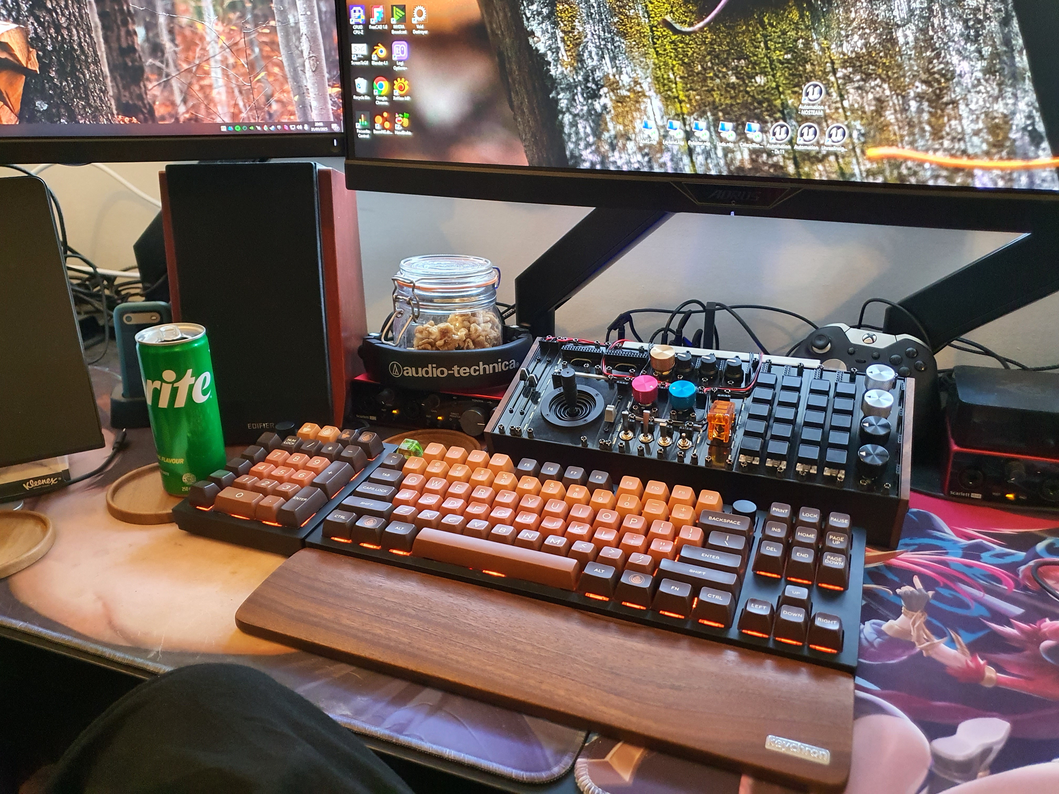
Docs/Logs/Log-9_011.jpg
