MostlyCoraGrace/EurorackButtonBoard/Docs/Logs/Log-10_001.png

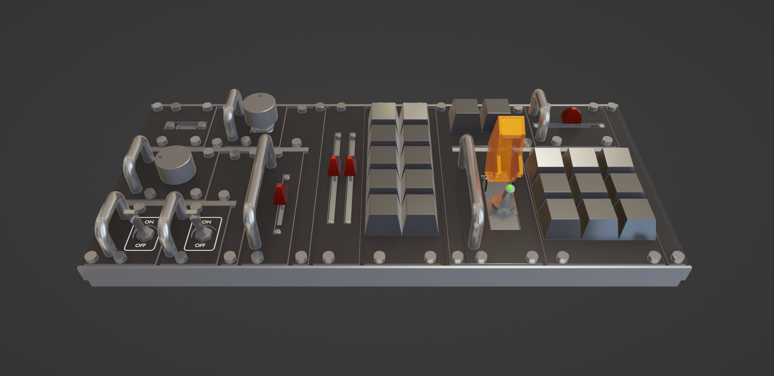
Docs/Logs/Log-10_001.png
