MostlyCoraGrace/EurorackButtonBoard/Docs/Logs/Log-10_002.jpg

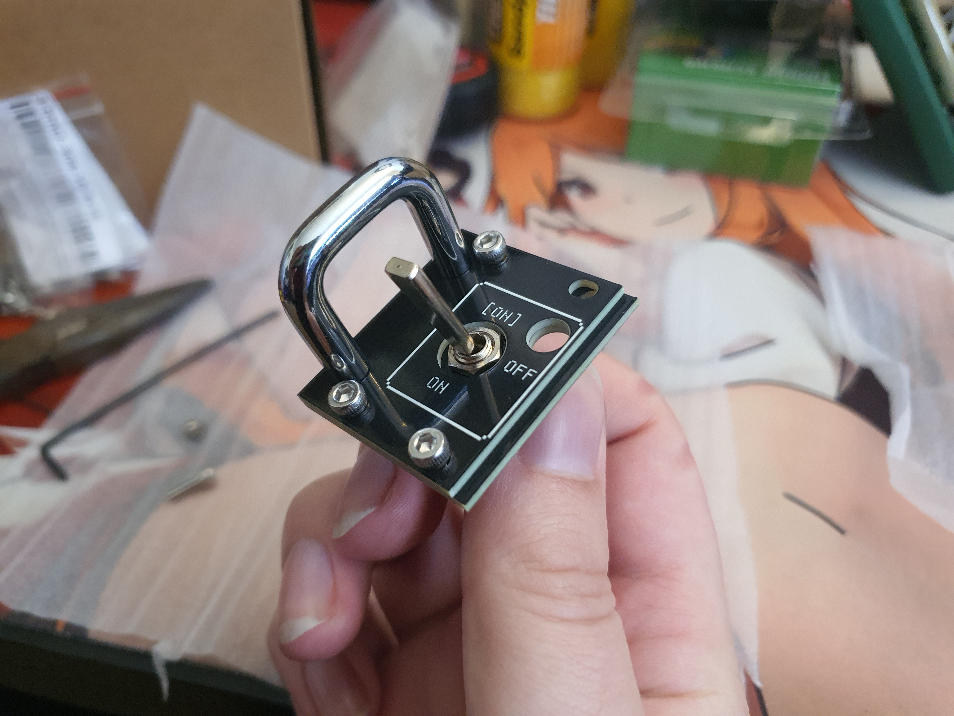
Docs/Logs/Log-10_002.jpg
