MostlyCoraGrace/EurorackButtonBoard/Docs/Logs/Log-10_003.jpg

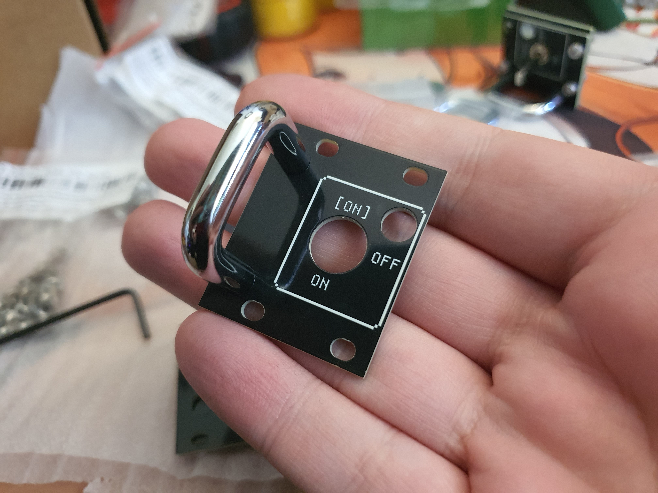
Docs/Logs/Log-10_003.jpg
