MostlyCoraGrace/EurorackButtonBoard/Docs/Logs/Log-10_004.jpg

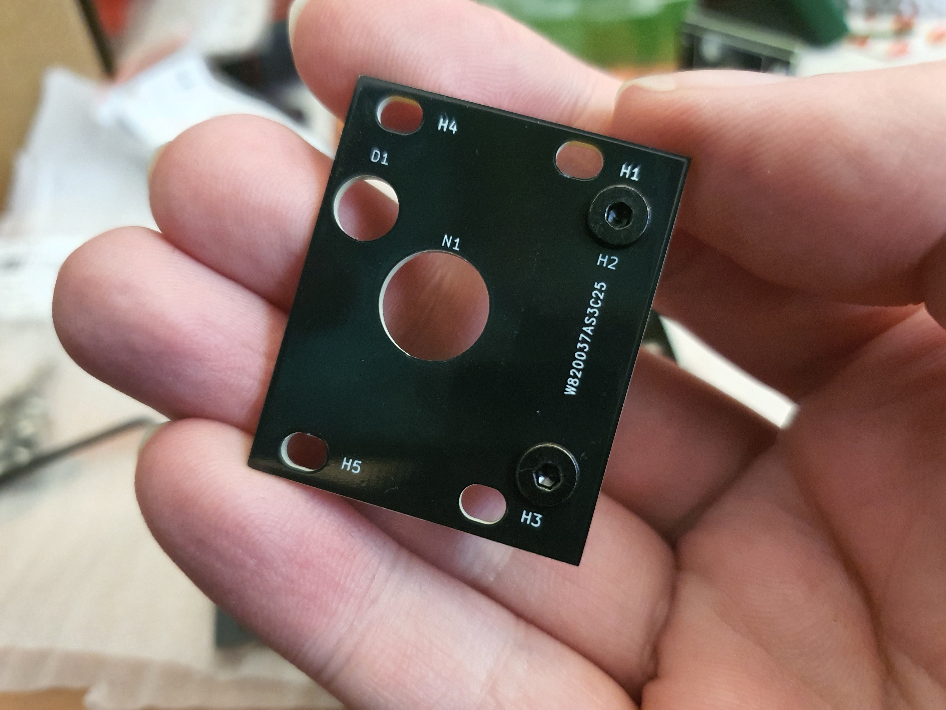
Docs/Logs/Log-10_004.jpg
