MostlyCoraGrace/EurorackButtonBoard/Docs/Logs/Log-10_005.jpg

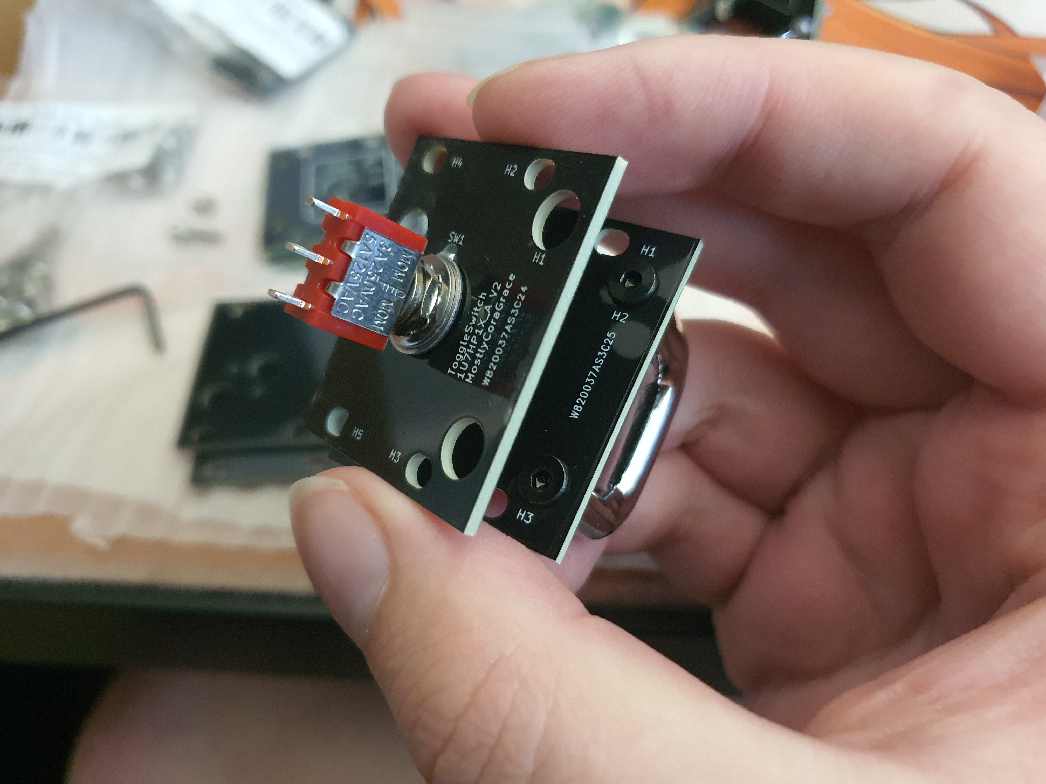
Docs/Logs/Log-10_005.jpg
