MostlyCoraGrace/EurorackButtonBoard/Docs/Logs/Log-10_006.jpg

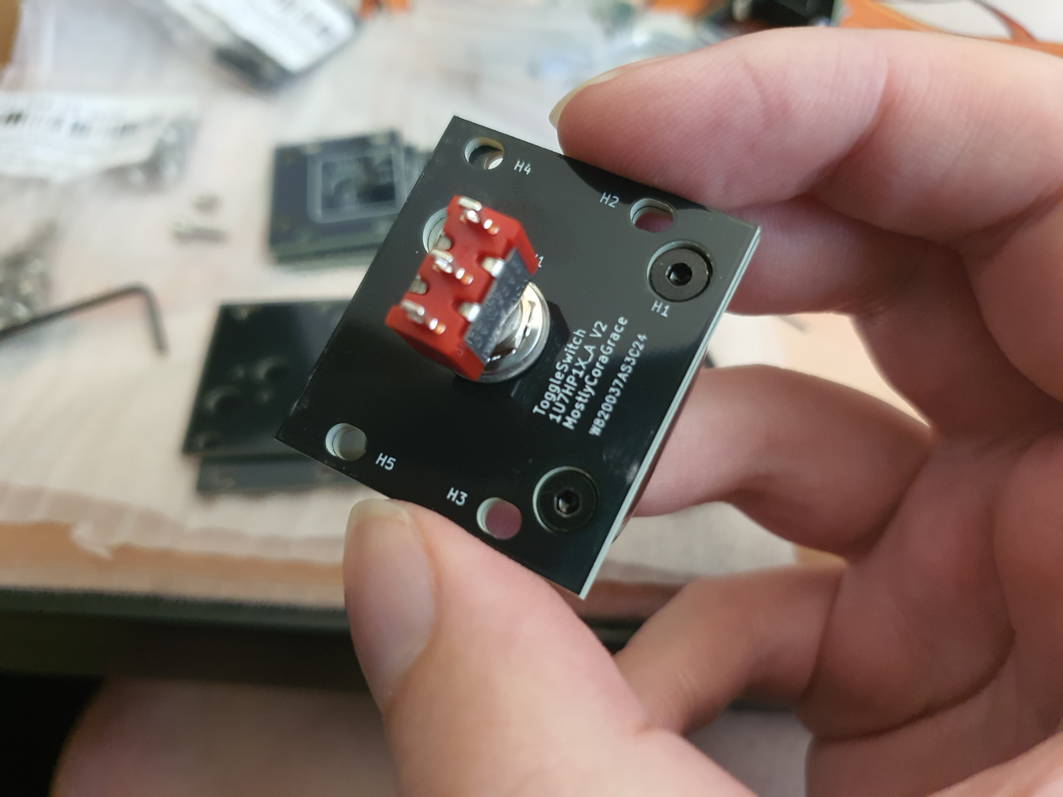
Docs/Logs/Log-10_006.jpg
