MostlyCoraGrace/EurorackButtonBoard/Docs/Logs/Log-10_007.jpg

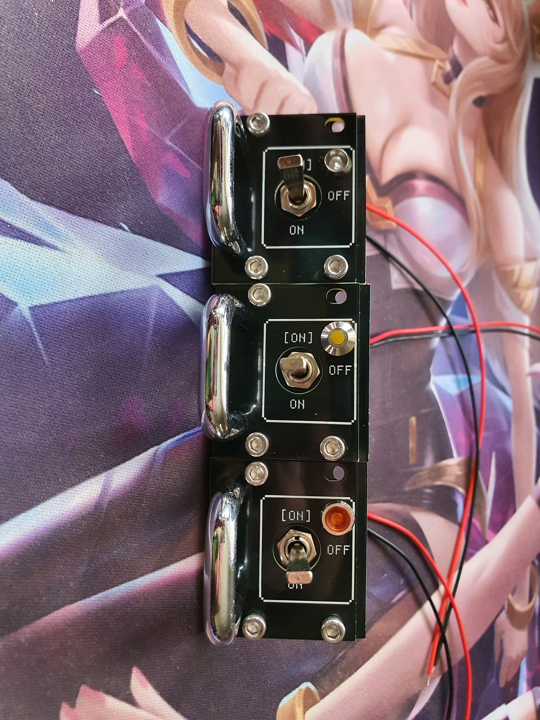
Docs/Logs/Log-10_007.jpg
