MostlyCoraGrace/EurorackButtonBoard/Docs/Logs/Log-10_008.jpg

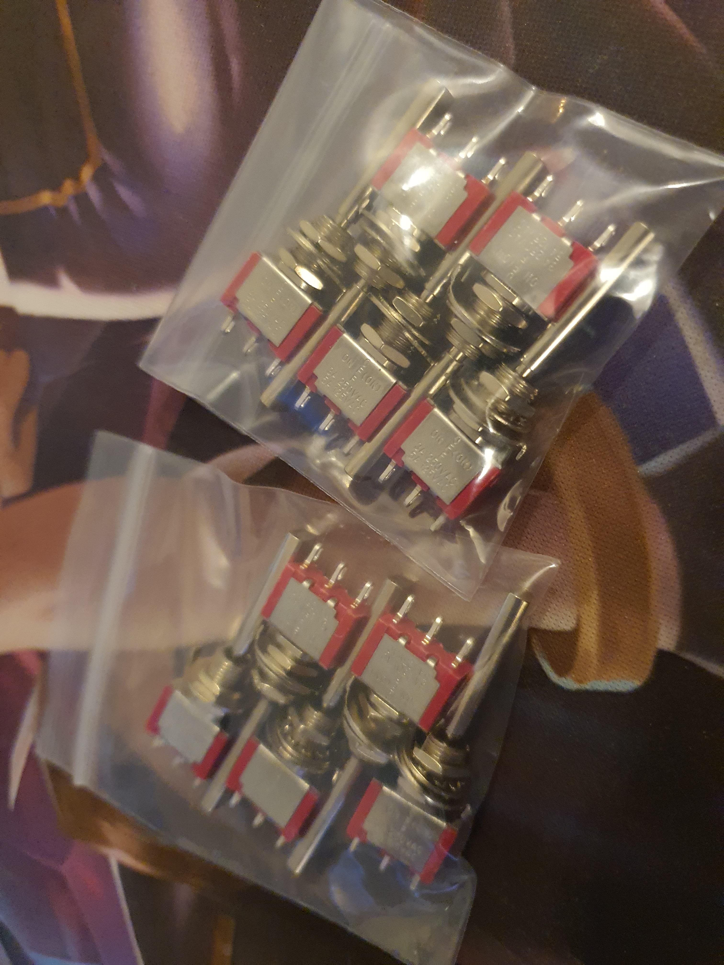
Docs/Logs/Log-10_008.jpg
