MostlyCoraGrace/EurorackButtonBoard/Docs/Logs/Screenshot 2025-03-05 171452.jpg

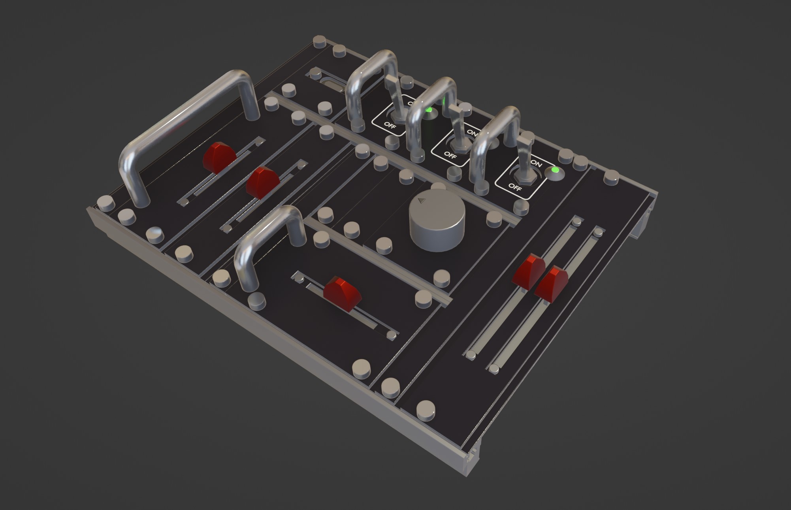
Docs/Logs/Screenshot 2025-03-05 171452.jpg
