MostlyCoraGrace/EurorackButtonBoard/Docs/Logs/Screenshot 2025-03-05 171511.jpg

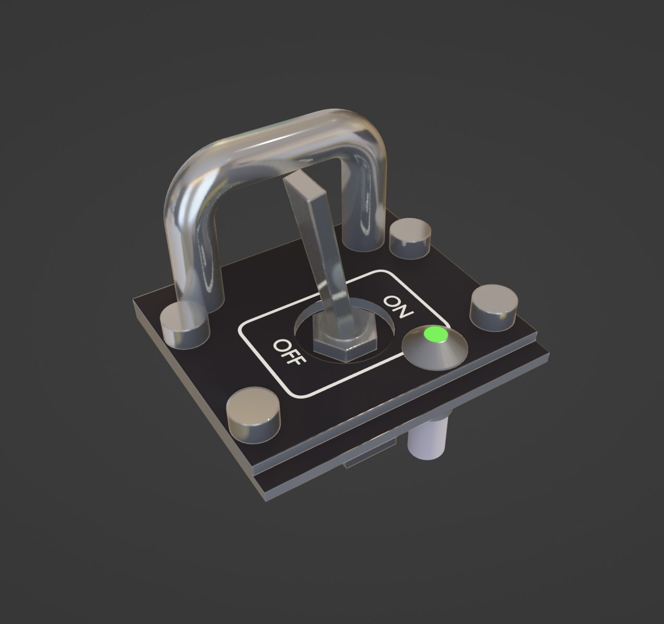
Docs/Logs/Screenshot 2025-03-05 171511.jpg
