MostlyCoraGrace/EurorackButtonBoard/Docs/Logs/Screenshot 2026-01-06 194159.png

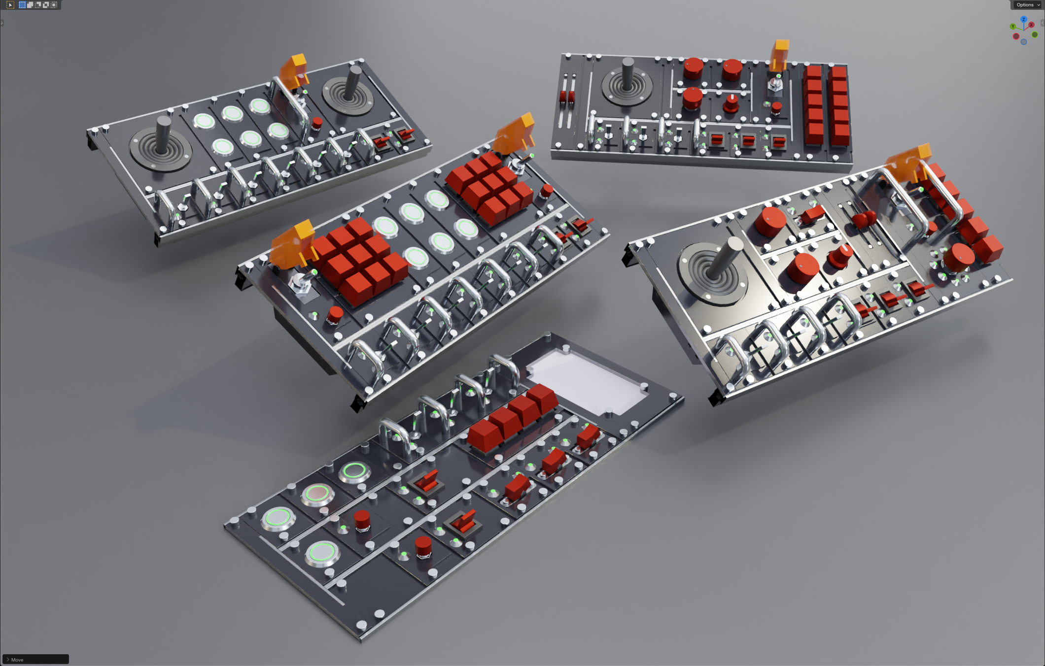
Docs/Logs/Screenshot 2026-01-06 194159.png
