MostlyCoraGrace/EurorackButtonBoard/Circuitpython/Controller01/boot.py

"""JoystickXL standard boot.py."""

import usb_hid  # type: ignore (this is a CircuitPython built-in)
from joystick_xl.hid import create_joystick

# This will enable all of the standard CircuitPython USB HID devices along with a
# USB HID joystick.
usb_hid.enable(
    (
        usb_hid.Device.KEYBOARD,
        usb_hid.Device.MOUSE,
        usb_hid.Device.CONSUMER_CONTROL,
        create_joystick(axes=8, buttons=128, hats=4),
    )
)
